Alexandros444/Datenbojen/docs/img/20250713_175419.jpg

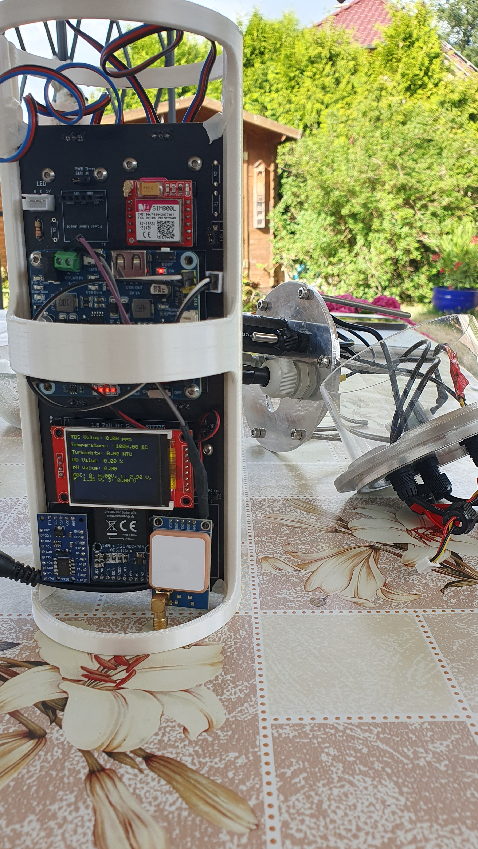
docs/img/20250713_175419.jpg
