Alexandros444/Datenbojen/docs/img/20250718_185127.jpg

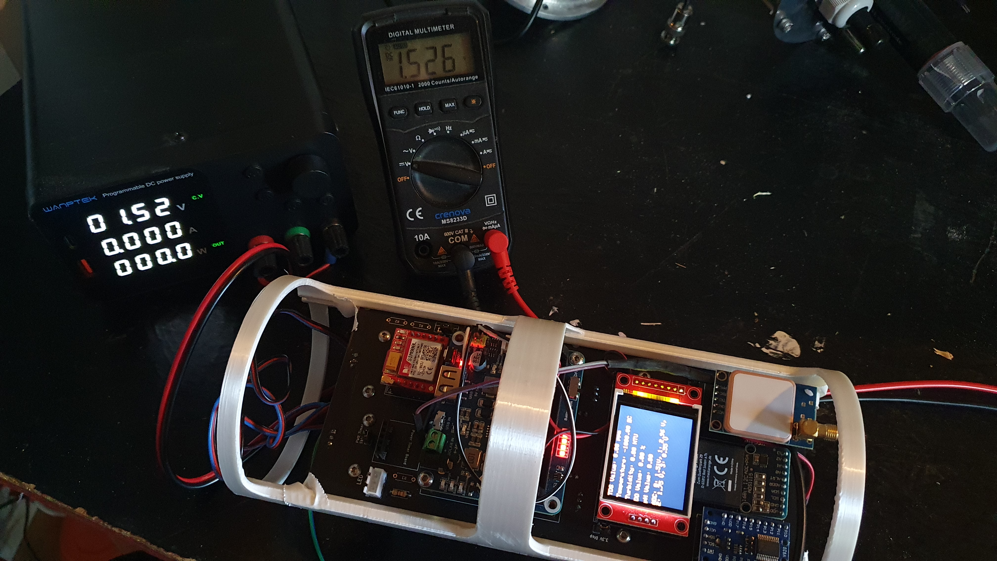
docs/img/20250718_185127.jpg
