Alexandros444/Datenbojen/docs/img/Entwurf/IMG_9408.jpg

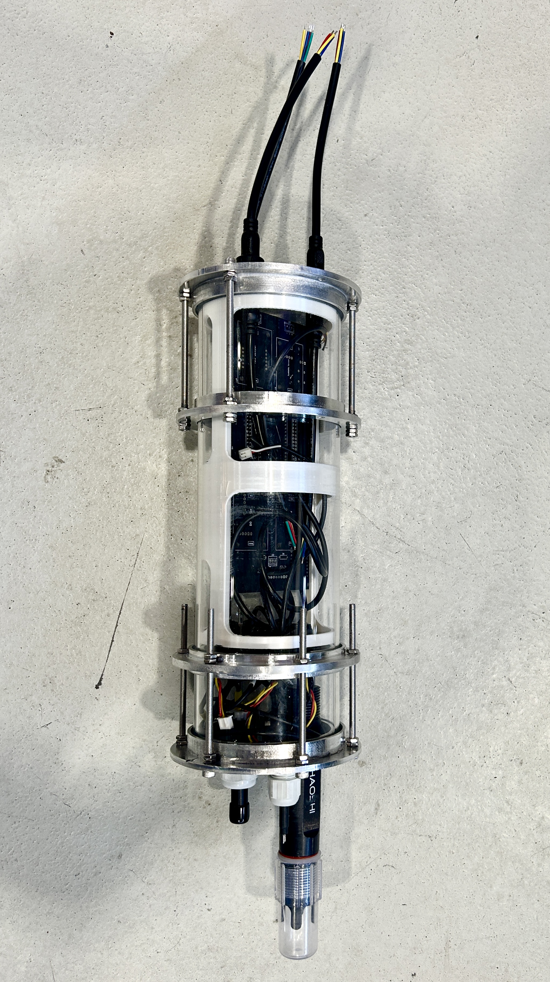
docs/img/Entwurf/IMG_9408.jpg
