Alexandros444/Datenbojen/docs/img/Entwurf/pcb_schematic.png

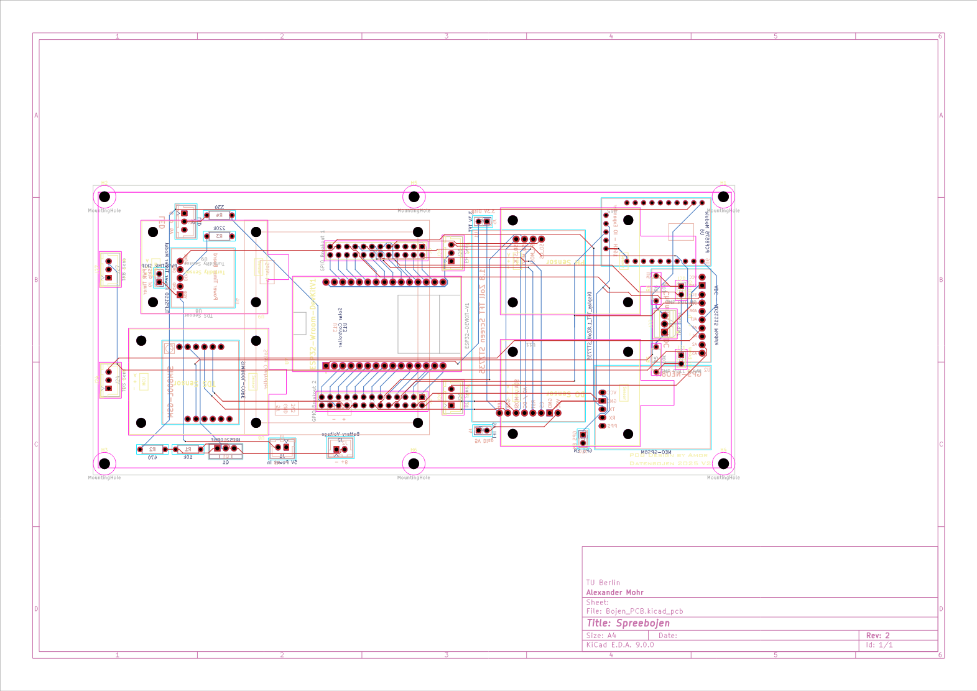
docs/img/Entwurf/pcb_schematic.png
