Alexandros444/Datenbojen/docs/img/Entwurf/pcb_vorderseite.jpg

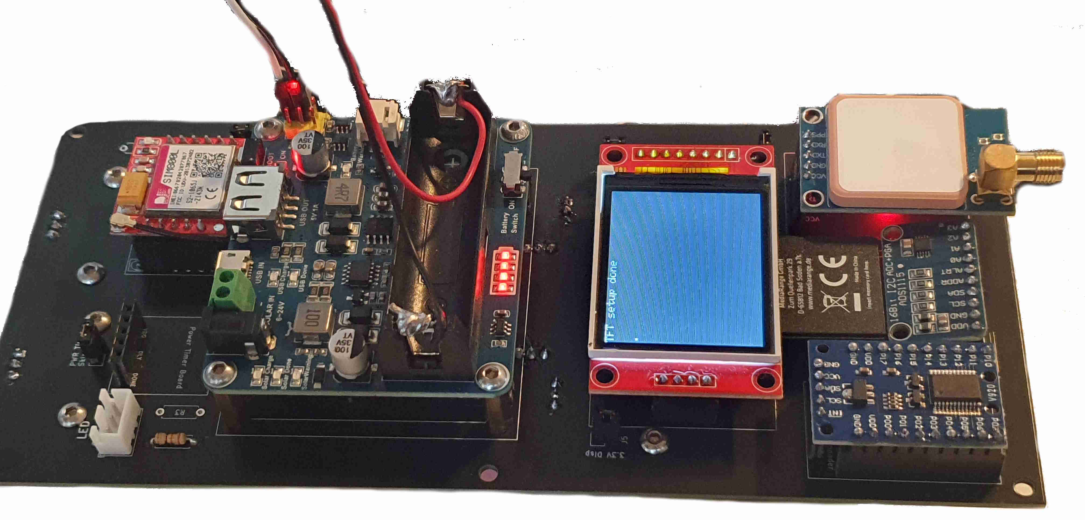
docs/img/Entwurf/pcb_vorderseite.jpg
