Alexandros444/Datenbojen/docs/img/Entwurf/pcb_with_sensors.jpg

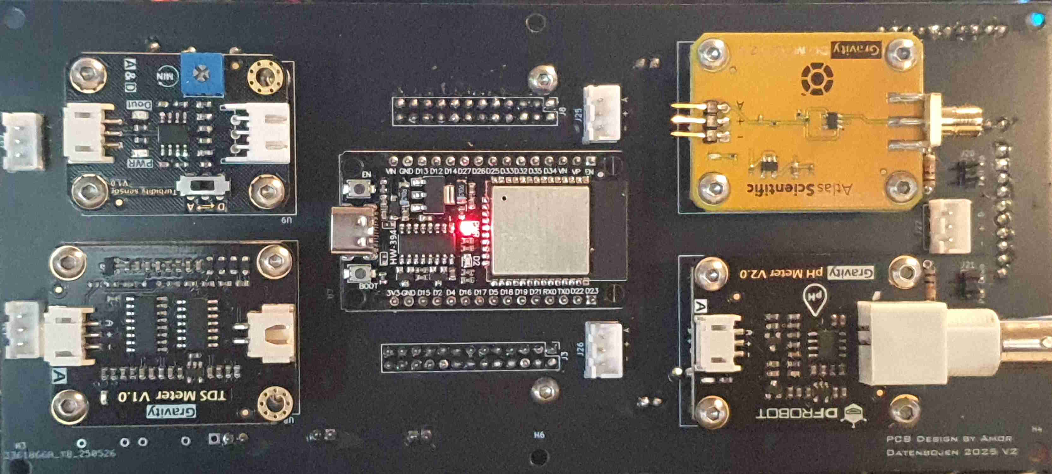
docs/img/Entwurf/pcb_with_sensors.jpg
