Alexandros444/Datenbojen/docs/img/Entwurf/Platine_PCB_Kicad.png

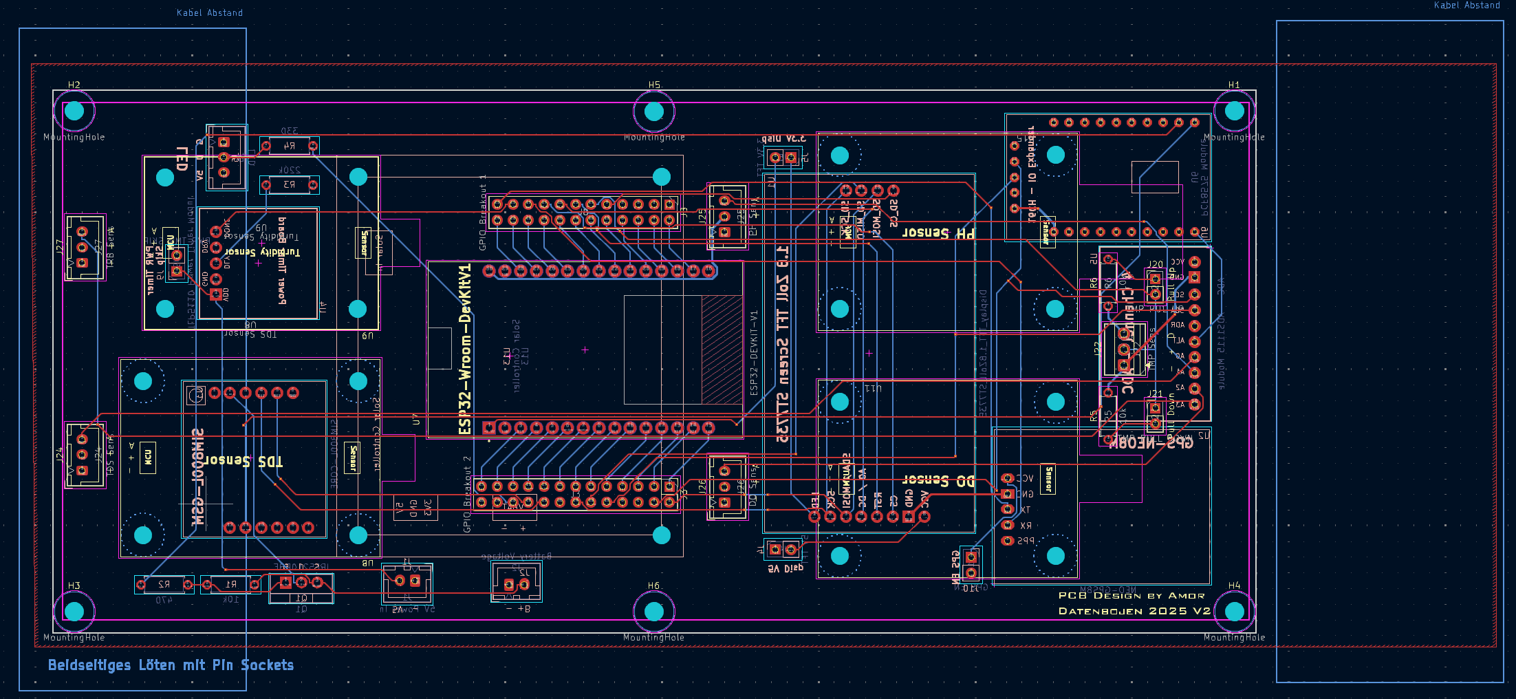
docs/img/Entwurf/Platine_PCB_Kicad.png
