Alexandros444/Datenbojen/docs/img/Entwurf/Platine_PCB_Kicad_3D.png

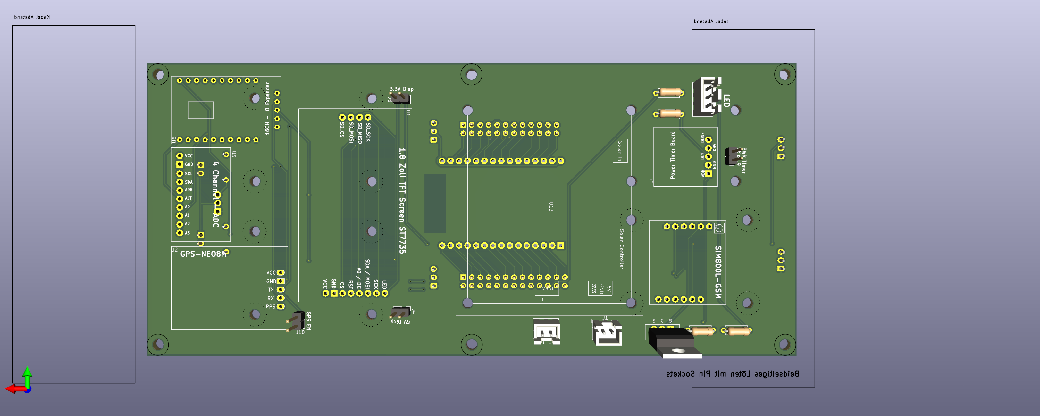
docs/img/Entwurf/Platine_PCB_Kicad_3D.png
