Alexandros444/Datenbojen/docs/img/Entwurf/Platine_PCB_Kicad_3D_render_cut.png

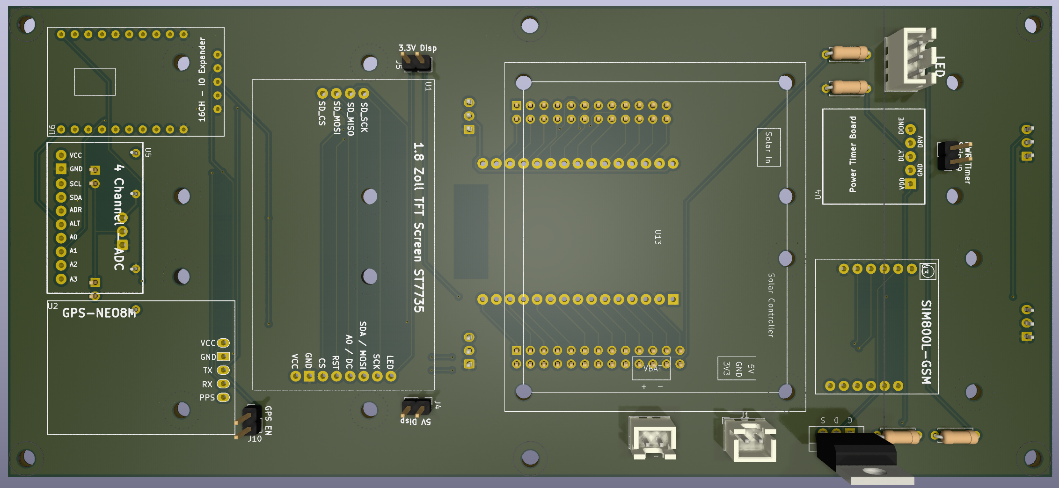
docs/img/Entwurf/Platine_PCB_Kicad_3D_render_cut.png
