Alexandros444/Datenbojen/docs/img/Entwurf/prototyp.jpg

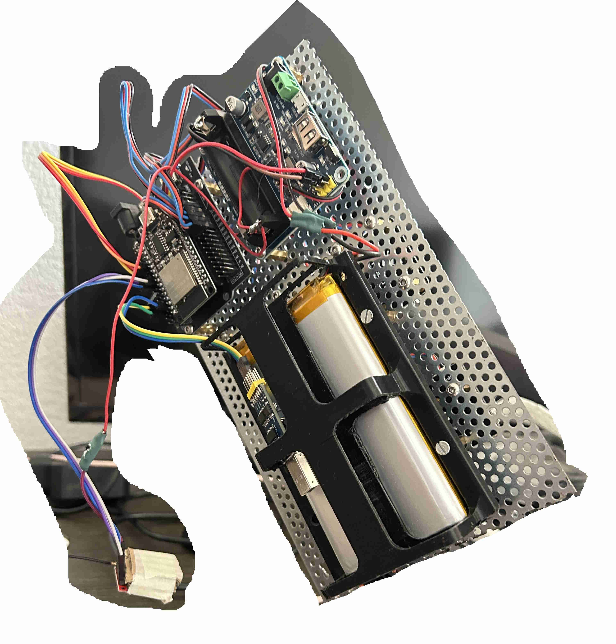
docs/img/Entwurf/prototyp.jpg
