Alexandros444/Datenbojen/docs/img/Entwurf/prototyp_nogb.png

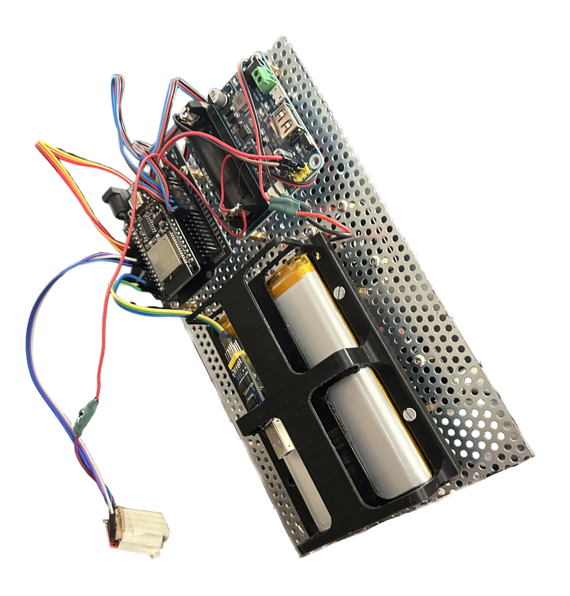
docs/img/Entwurf/prototyp_nogb.png
