Alexandros444/Datenbojen/docs/img/Entwurf/©TheresaMariaForthaus-53677.jpg

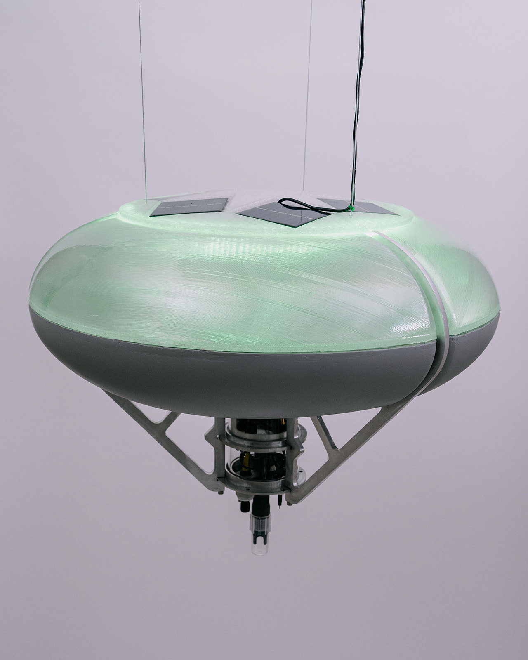
docs/img/Entwurf/©TheresaMariaForthaus-53677.jpg
