Alexandros444/Datenbojen/docs/img/Entwurf/©TheresaMariaForthaus-53696.jpg

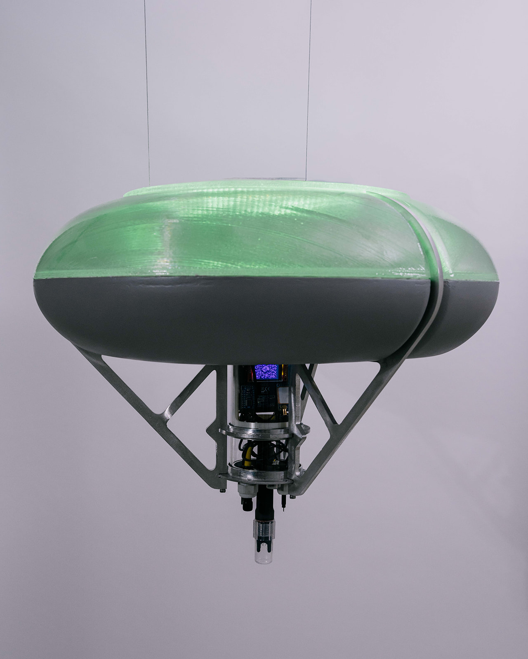
docs/img/Entwurf/©TheresaMariaForthaus-53696.jpg
