Alexandros444/Datenbojen/docs/img/Entwurf/©TheresaMariaForthaus-53716.jpg

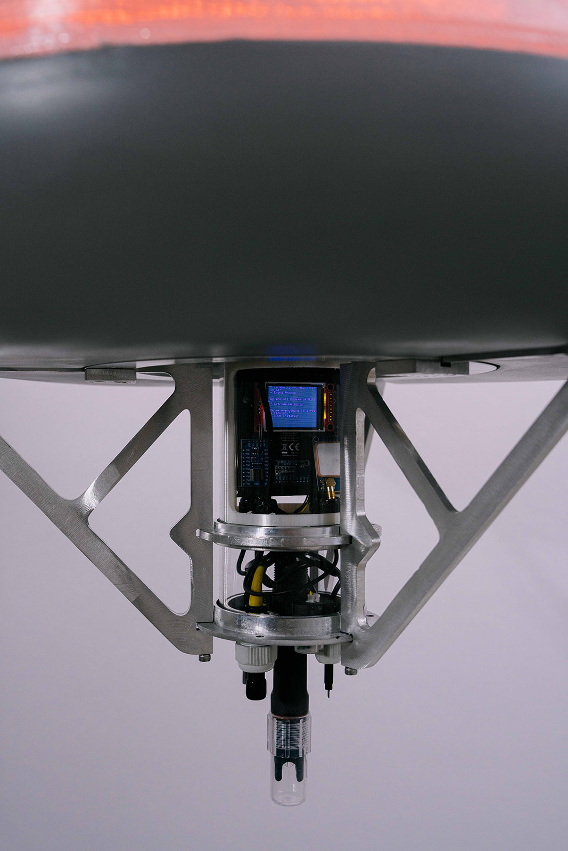
docs/img/Entwurf/©TheresaMariaForthaus-53716.jpg
