Alexandros444/Datenbojen/docs/img/Entwurf/©TheresaMariaForthaus-53720.jpg

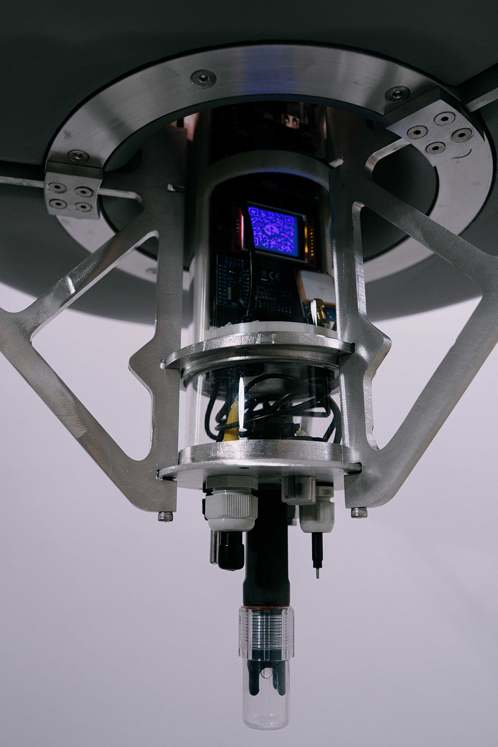
docs/img/Entwurf/©TheresaMariaForthaus-53720.jpg
