Alexandros444/Datenbojen/docs/img/Entwurf/©TheresaMariaForthaus-53730.jpg

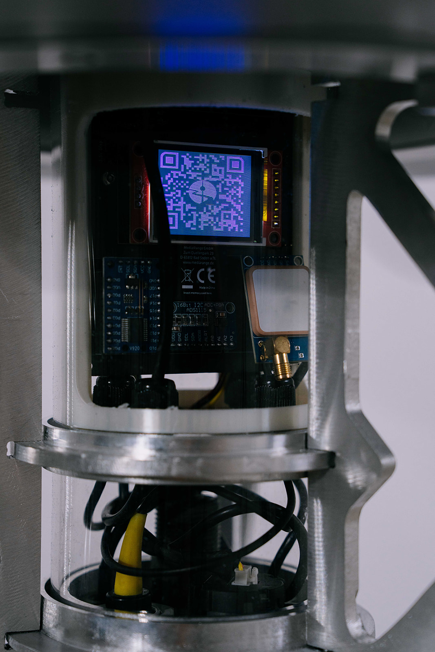
docs/img/Entwurf/©TheresaMariaForthaus-53730.jpg
