Alexandros444/Datenbojen/docs/img/iteration 3/20251018_173604.jpg

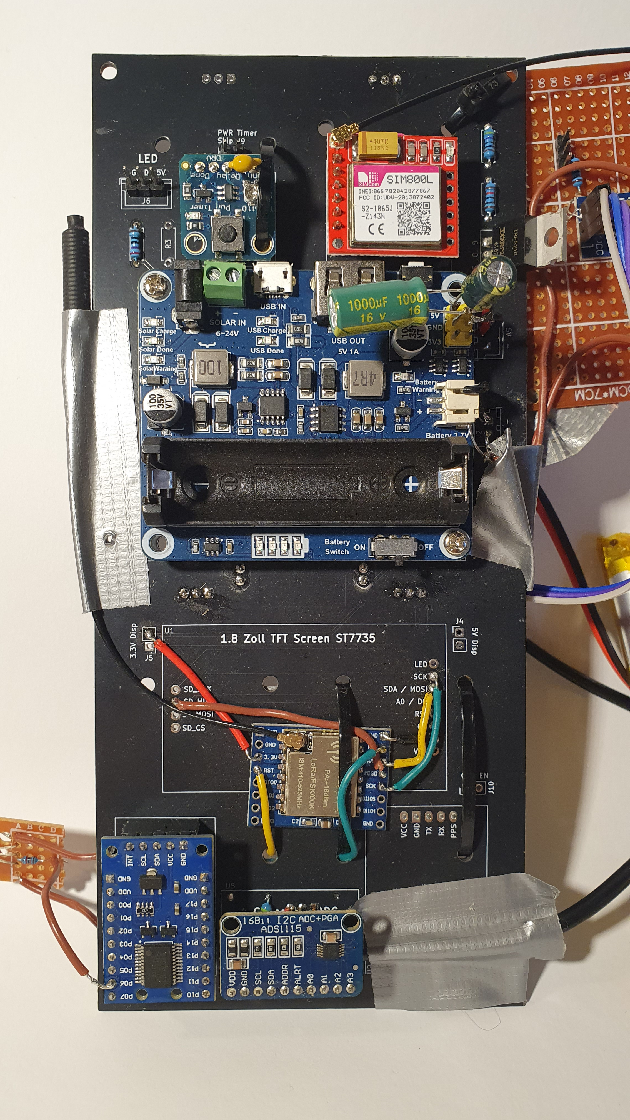
docs/img/iteration 3/20251018_173604.jpg
