Alexandros444/Datenbojen/docs/img/iteration 3/20251018_173955.jpg

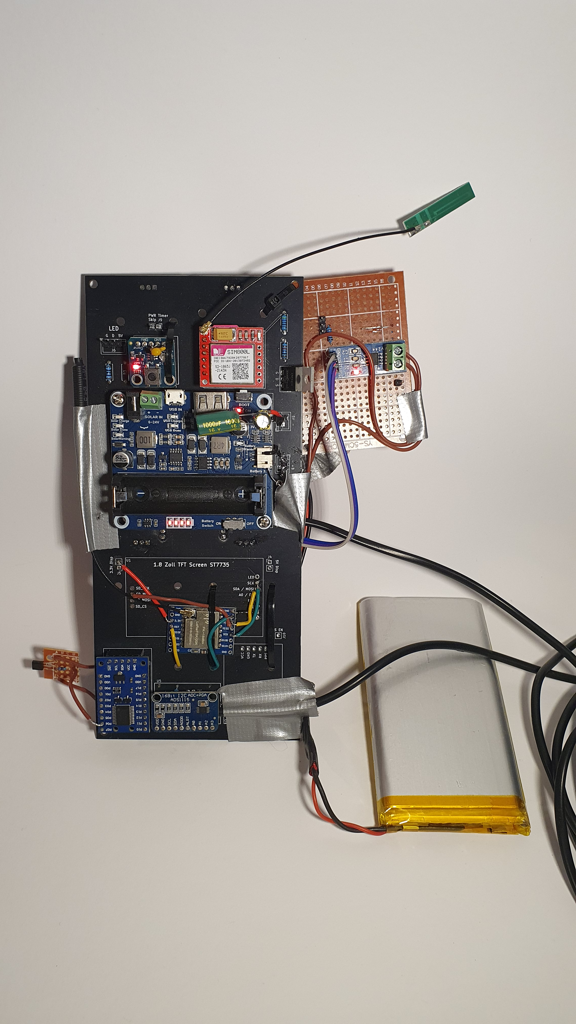
docs/img/iteration 3/20251018_173955.jpg
