Alexandros444/Datenbojen/docs/img/iteration 3/20251018_174100.jpg

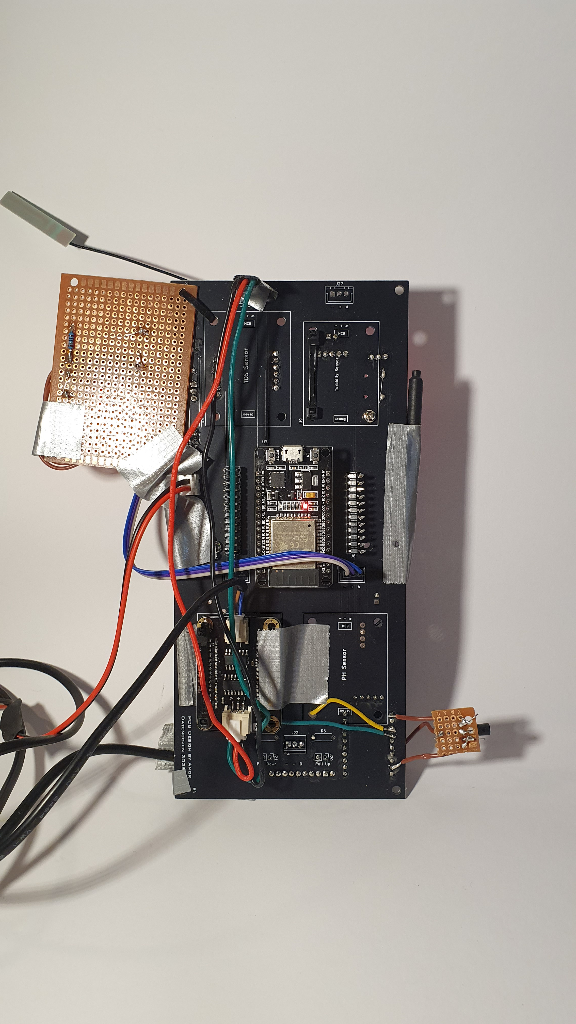
docs/img/iteration 3/20251018_174100.jpg
