Alexandros444/Datenbojen/docs/img/pcb_TPL5110.png

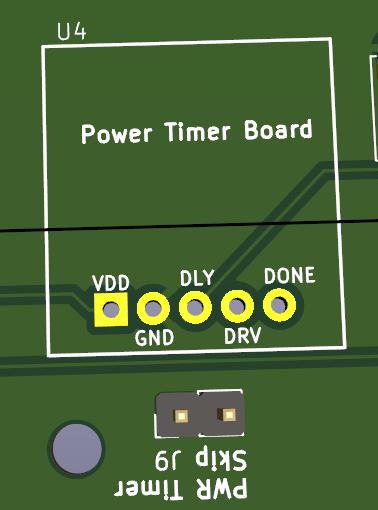
docs/img/pcb_TPL5110.png
