Alexandros444/Datenbojen/docs/img/pcbb.png

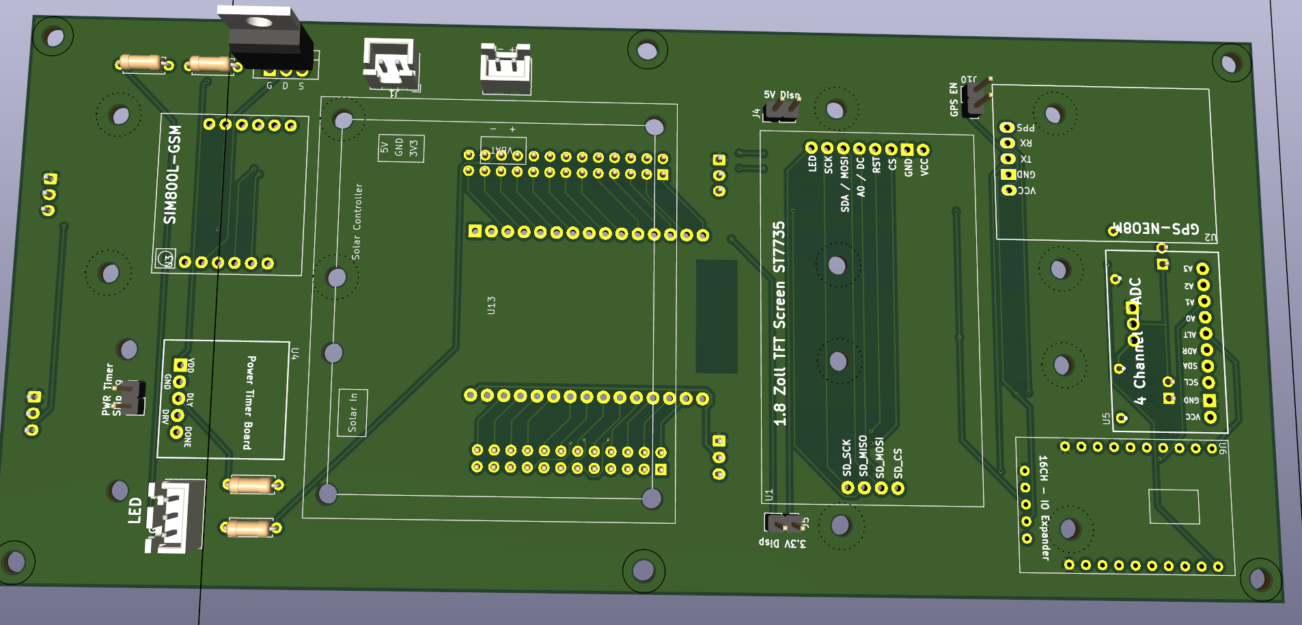
docs/img/pcbb.png
