Alexandros444/Datenbojen/docs/img/pcbf.png

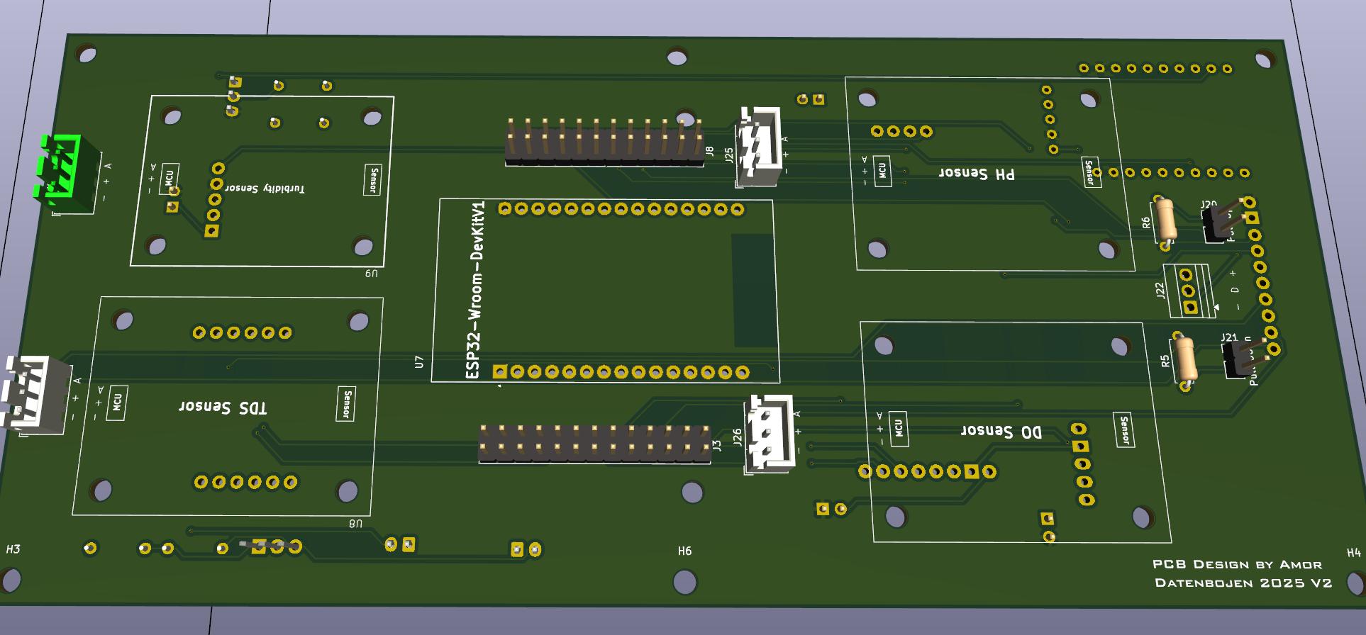
docs/img/pcbf.png
