Alexandros444/Datenbojen/docs/img/schaltplan_esp.png

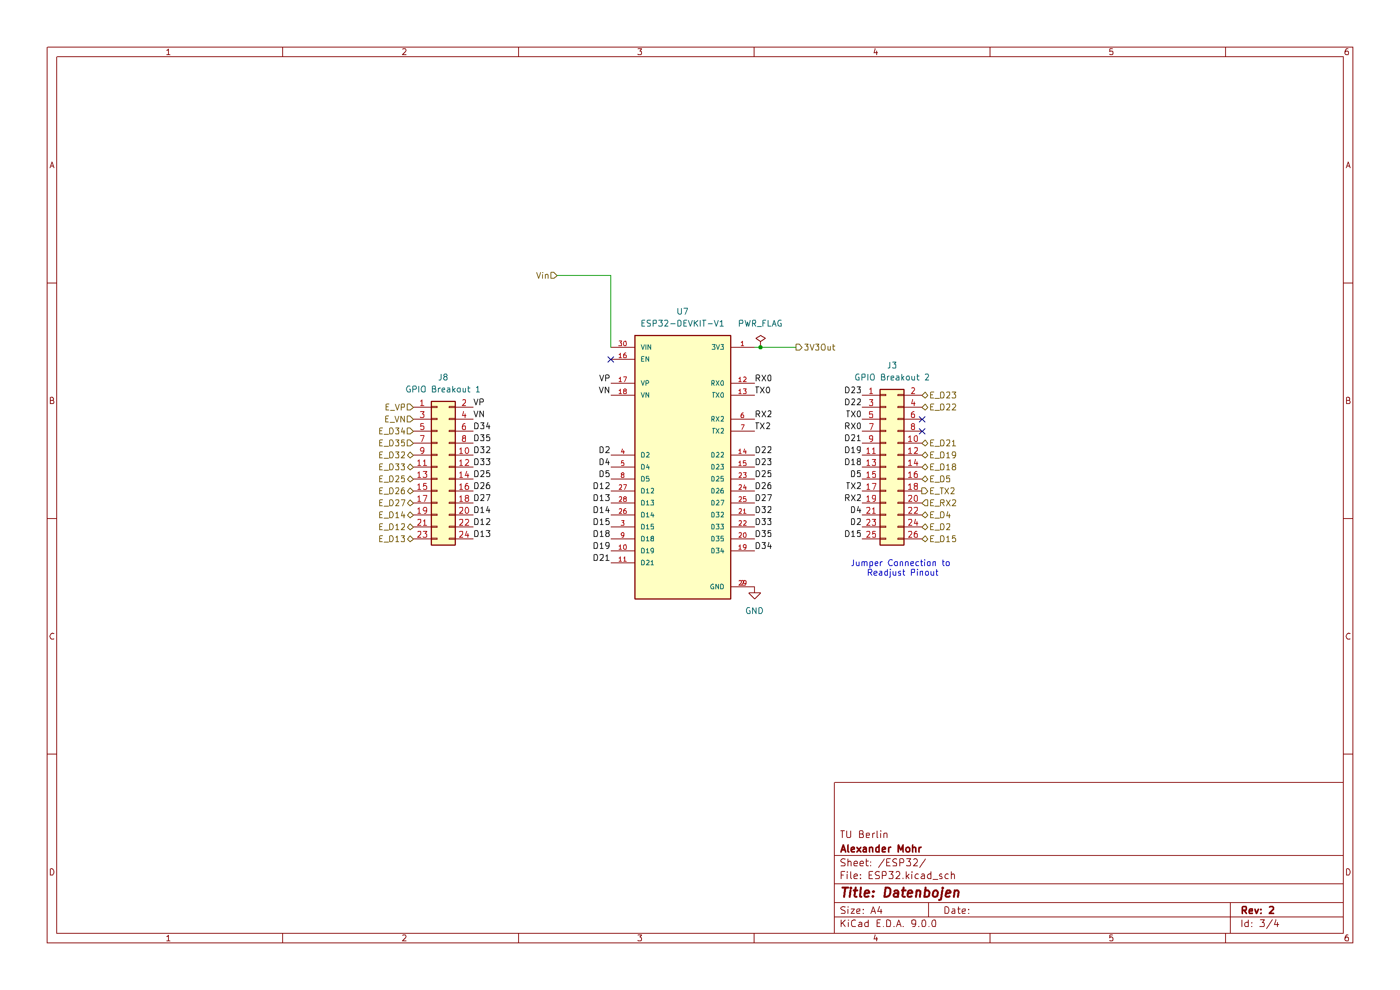
docs/img/schaltplan_esp.png
