Alexandros444/Datenbojen/docs/img/schaltplan_gesamt.png

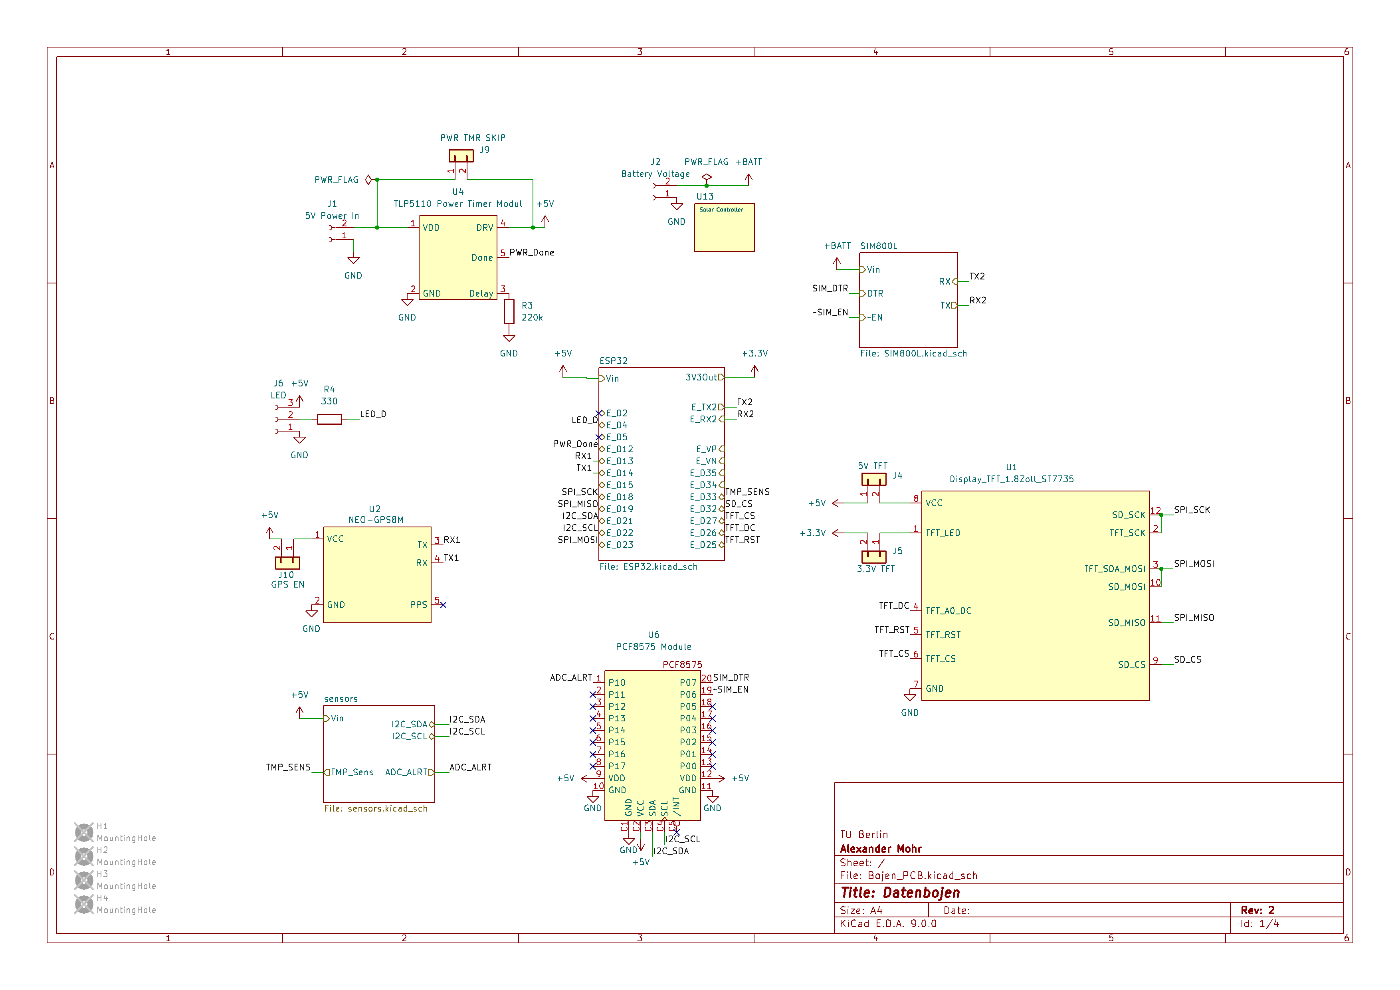
docs/img/schaltplan_gesamt.png
