Alexandros444/Datenbojen/docs/img/schaltplan_sensor.png

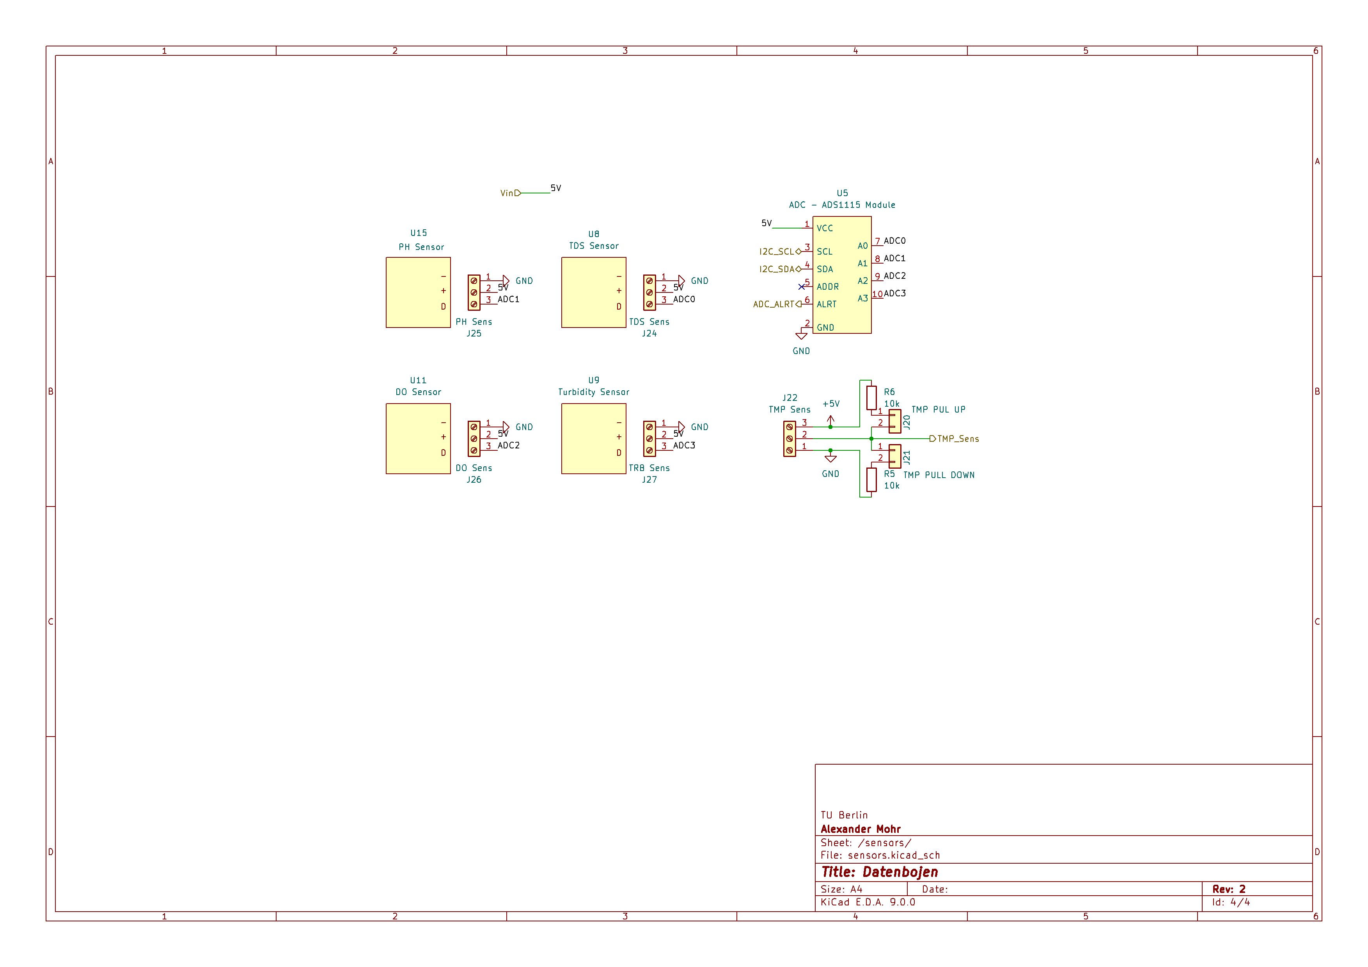
docs/img/schaltplan_sensor.png
