Alexandros444/Datenbojen/docs/img/schaltplan_sim.png

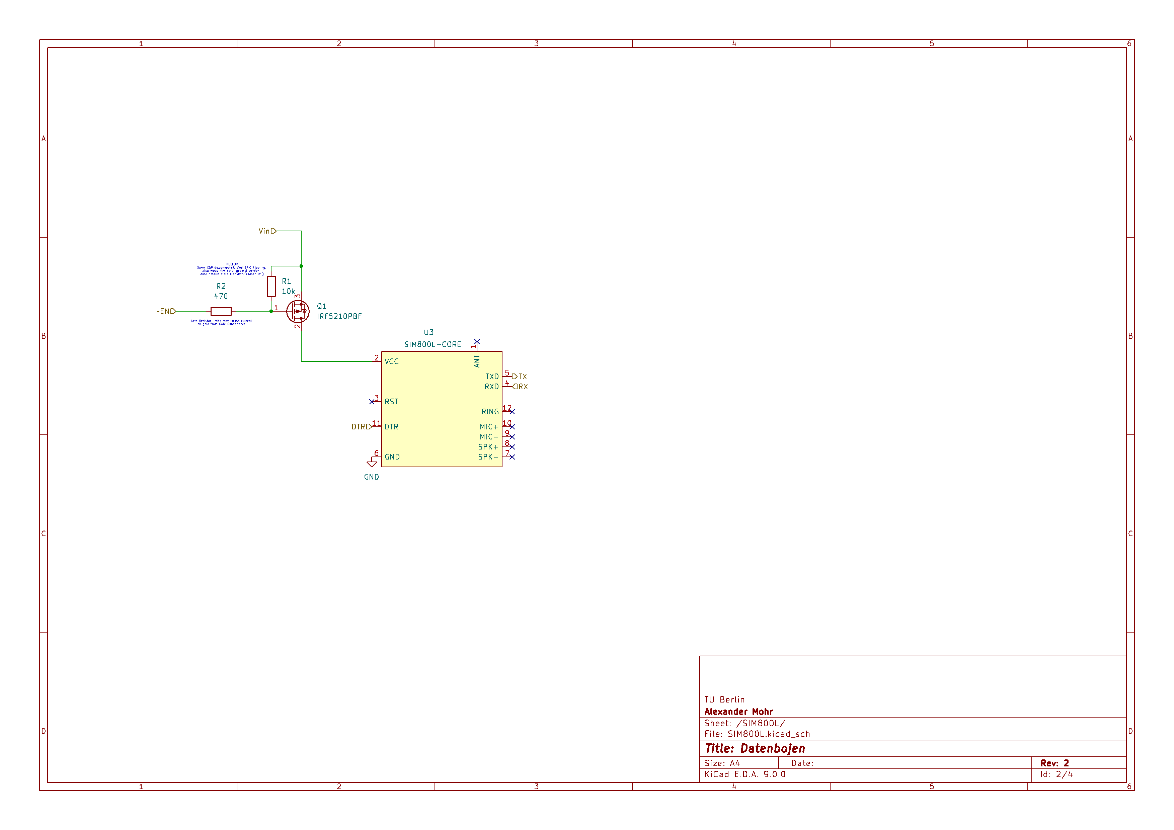
docs/img/schaltplan_sim.png
