Alexandros444/Datenbojen/docs/img/schematic_TPL5110.png

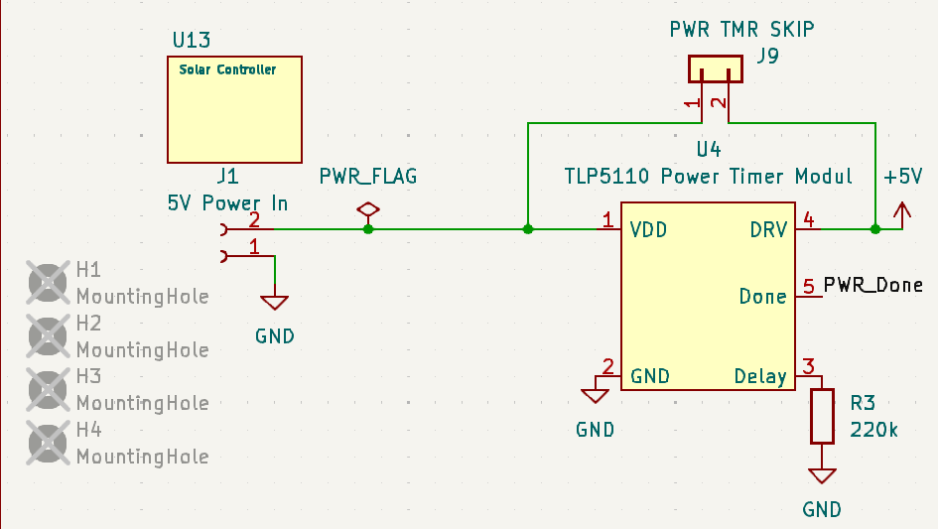
docs/img/schematic_TPL5110.png
