Alexandros444/Datenbojen/docs/img/server_data_plot.png

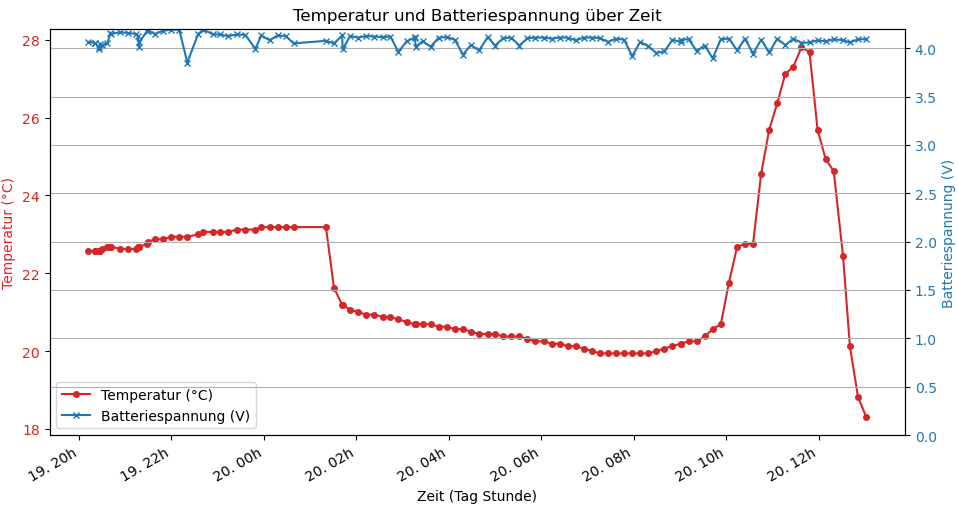
docs/img/server_data_plot.png
