Alexandros444/Datenbojen/docs/img/server_data_plot_2.png

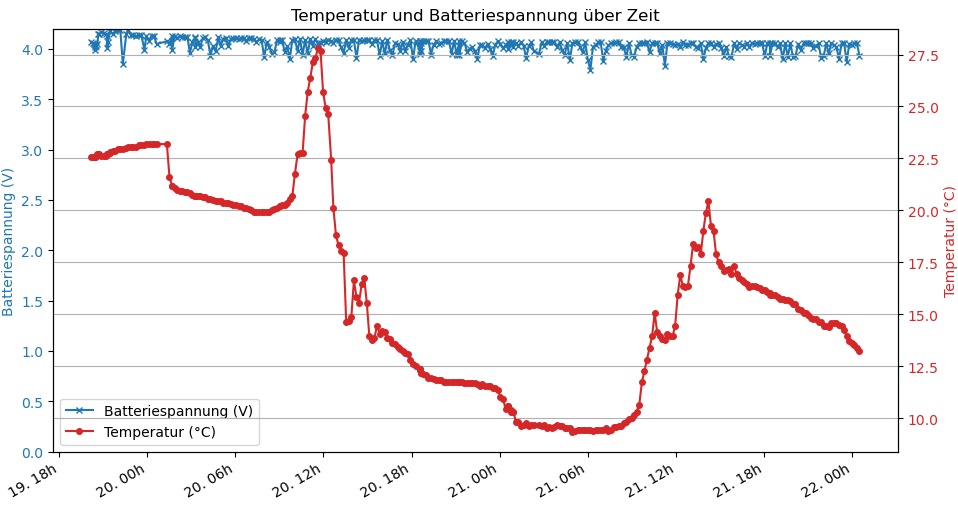
docs/img/server_data_plot_2.png
