Alexandros444/Datenbojen/docs/img/server_data_plot_3.png

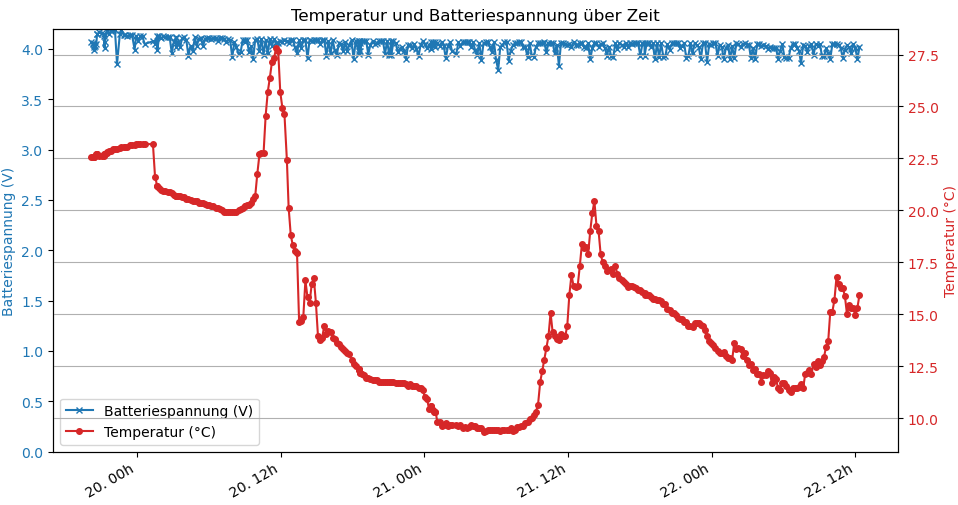
docs/img/server_data_plot_3.png
