Alexandros444/Datenbojen/docs/img/server_data_plot_4.png

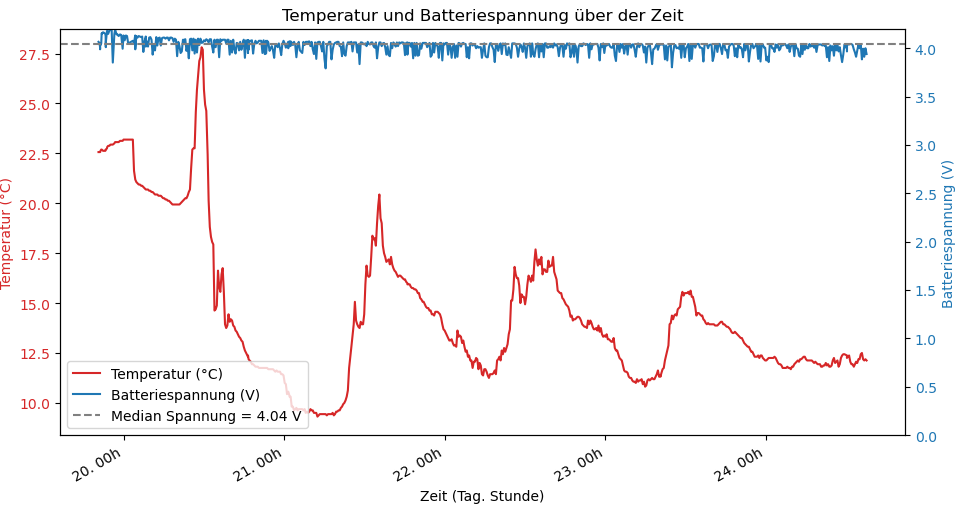
docs/img/server_data_plot_4.png
