Alexandros444/Datenbojen/docs/img/solar_charge_footprint.png

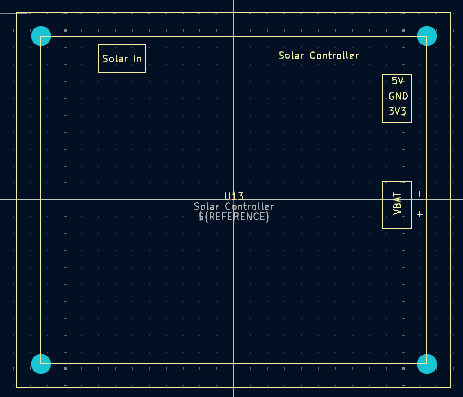
docs/img/solar_charge_footprint.png
