Alexandros444/Datenbojen/docs/img/solar_charge_schematic.png

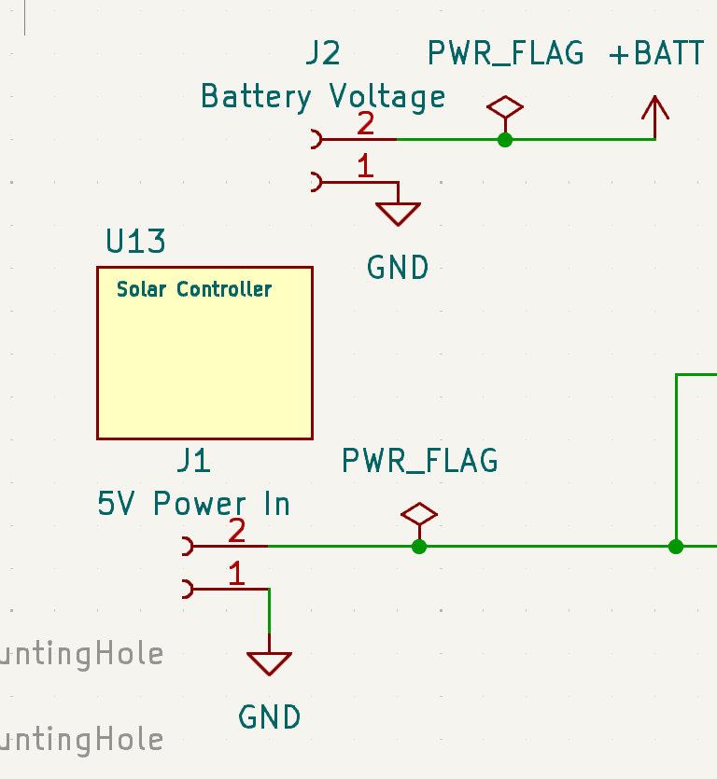
docs/img/solar_charge_schematic.png
