Alexandros444/Datenbojen/docs/img/solarmessung.png

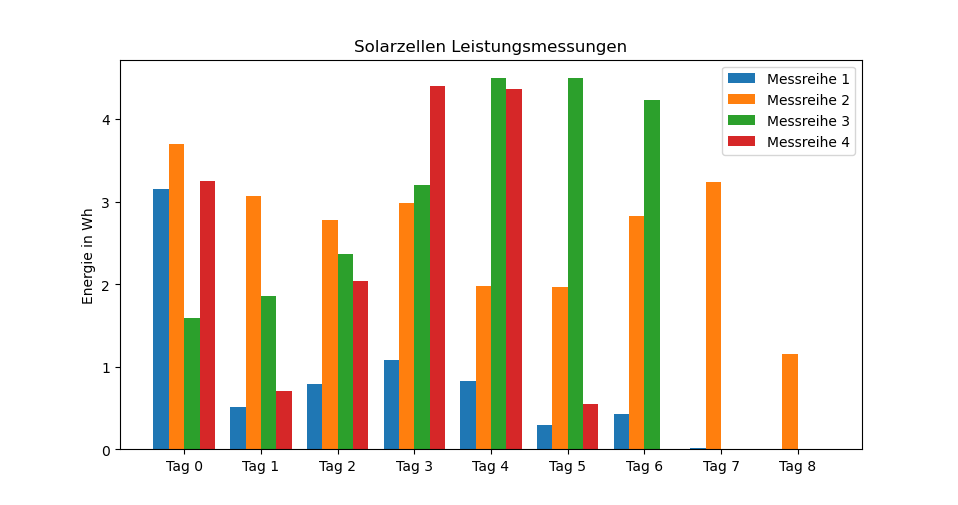
docs/img/solarmessung.png
