Alexandros444/Datenbojen/docs/img/verbrauch_1_messsend.png

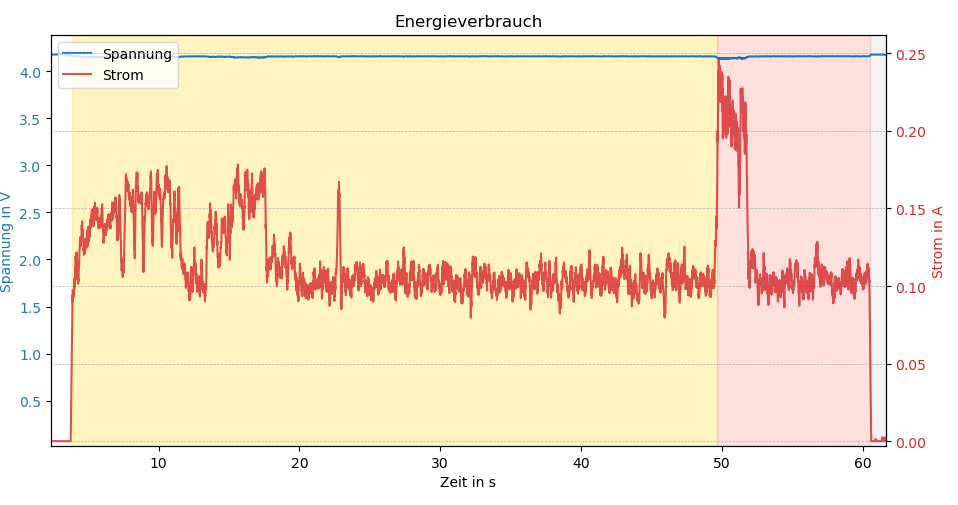
docs/img/verbrauch_1_messsend.png
