Alexandros444/Datenbojen/docs/img/verbrauch_1_zyklus.png

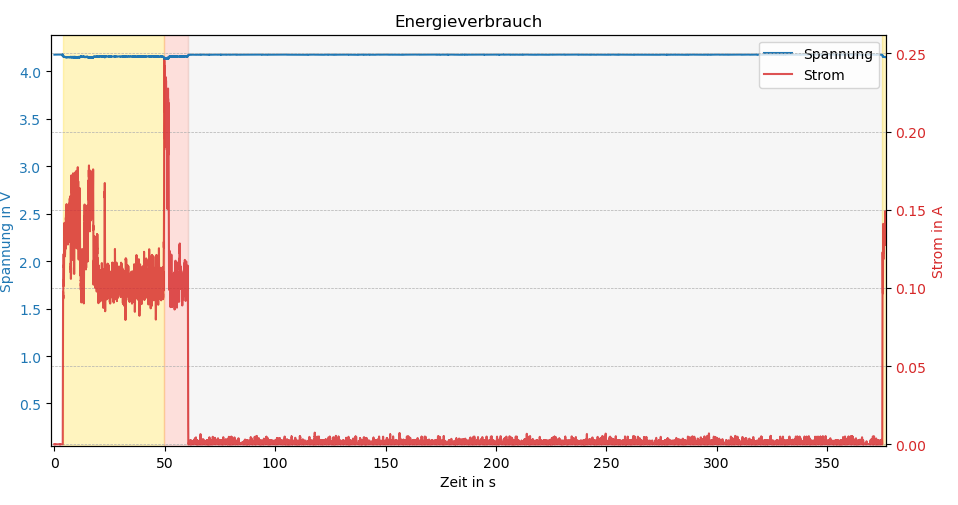
docs/img/verbrauch_1_zyklus.png
