Alexandros444/Datenbojen/docs/img/verbrauch_1_zyklus_mittel.png

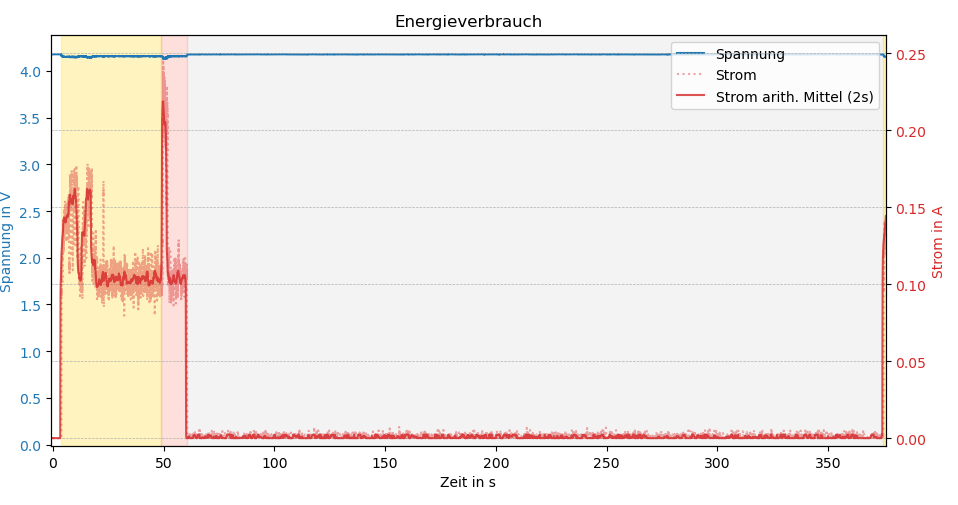
docs/img/verbrauch_1_zyklus_mittel.png
