Alexandros444/Datenbojen/docs/img/verbrauch_3_zyklen2.png

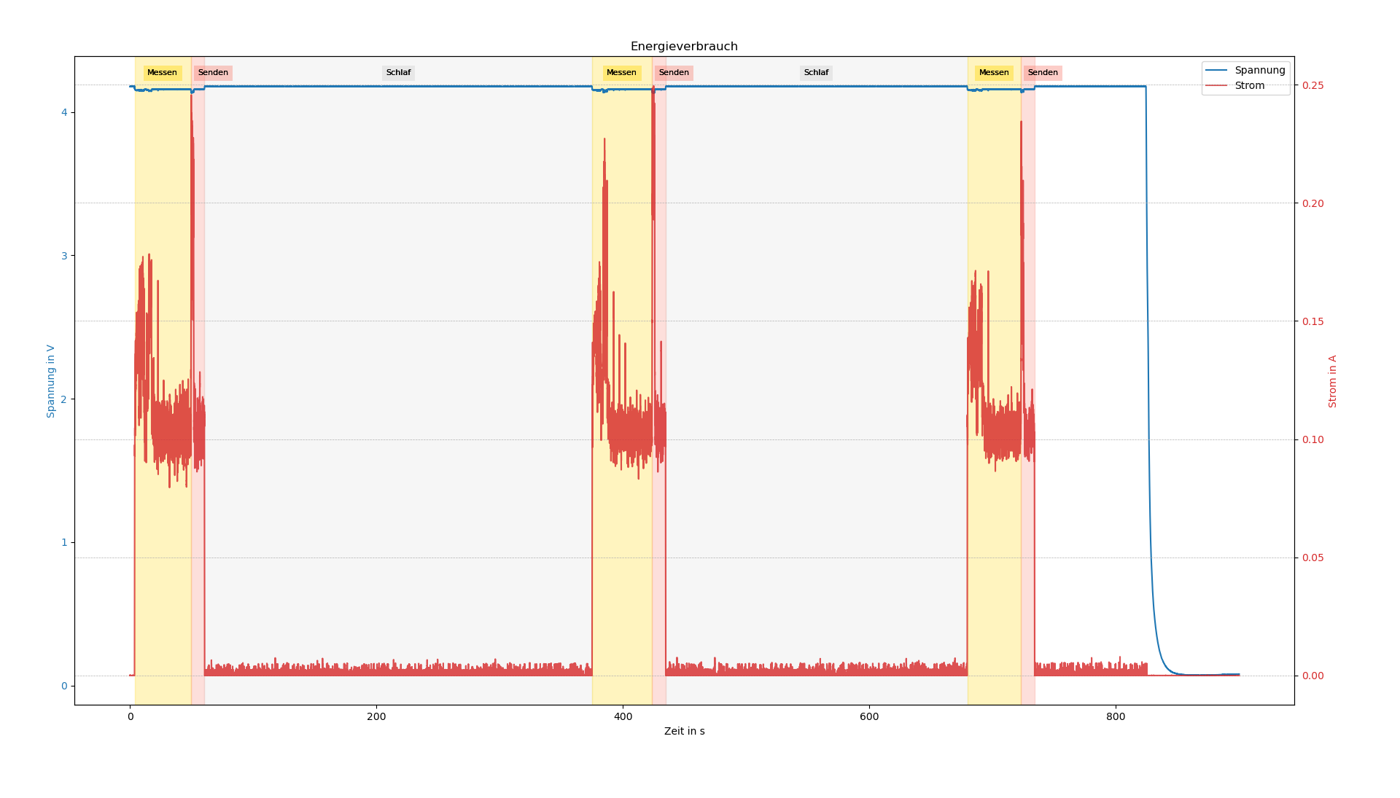
docs/img/verbrauch_3_zyklen2.png
