Alexandros444/Datenbojen/docs/img/verbrauch_3_zyklen_mittel.png

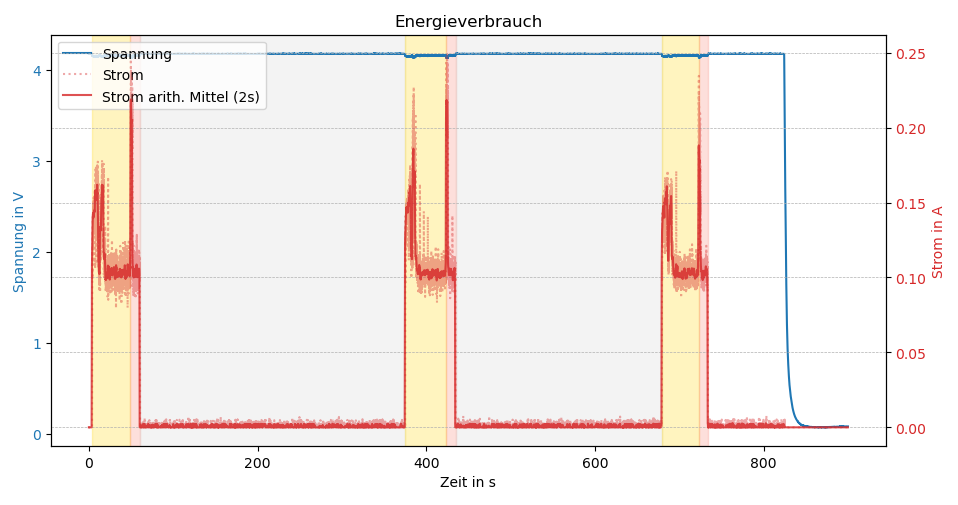
docs/img/verbrauch_3_zyklen_mittel.png
