Alexandros444/Datenbojen/docs/img/verbrauch_3_zyklen_mittel_cut.png

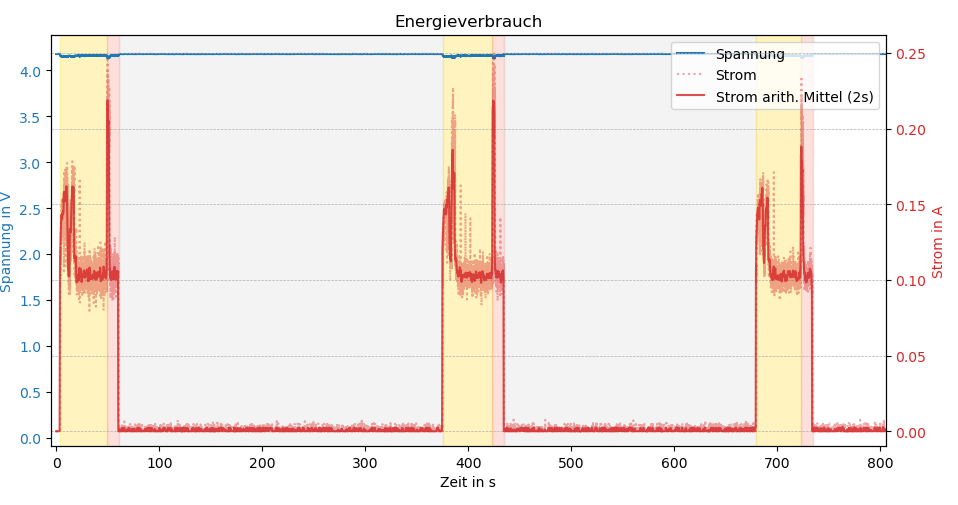
docs/img/verbrauch_3_zyklen_mittel_cut.png
