Alexandros444/Datenbojen/docs/img/verbrauch_3_zyklen_no_drop.png

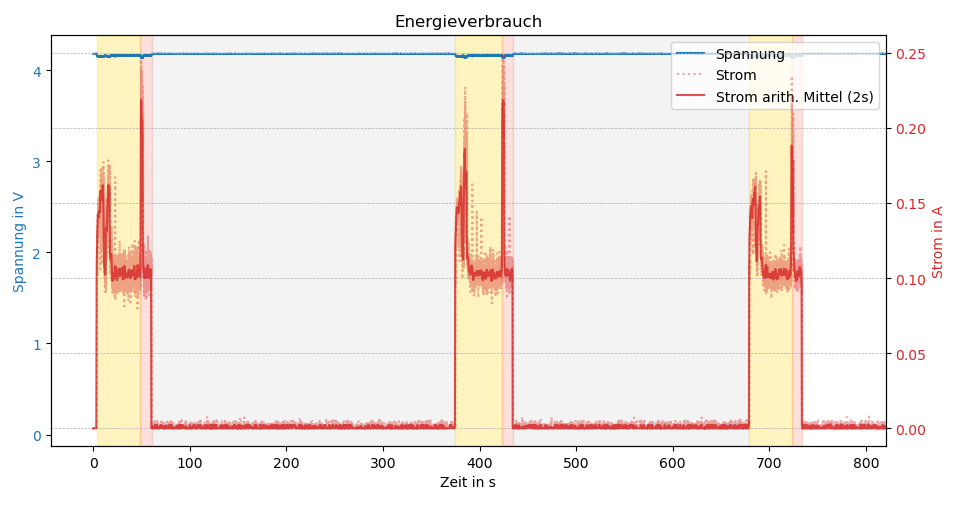
docs/img/verbrauch_3_zyklen_no_drop.png
