Alexandros444/Datenbojen/docs/img/verbrauch_akkumuliert_1_zyklus.png

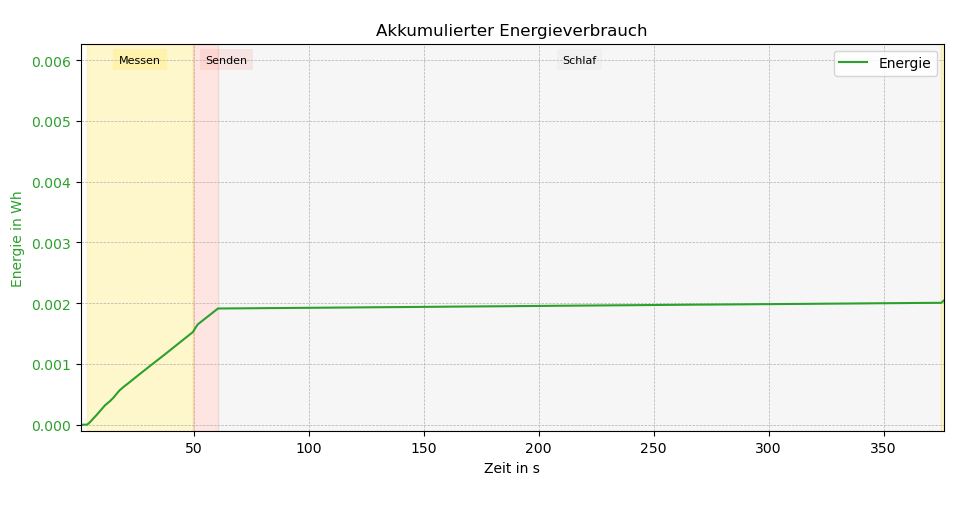
docs/img/verbrauch_akkumuliert_1_zyklus.png
