Alexandros444/Datenbojen/docs/img/verbrauch_akkumuliert_3_zyklen.png

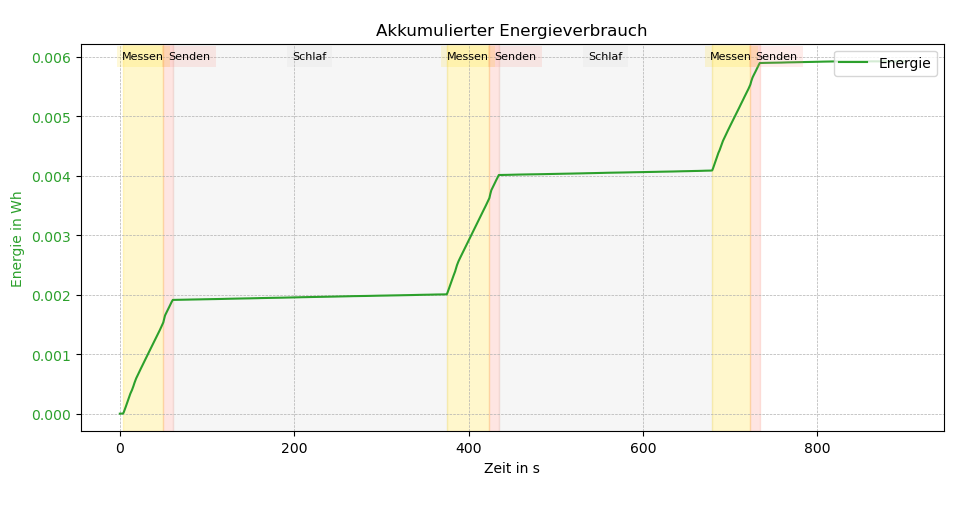
docs/img/verbrauch_akkumuliert_3_zyklen.png
