Alexandros444/Datenbojen/docs/img/verbrauch_akkumuliert_3_zyklen_cut.png

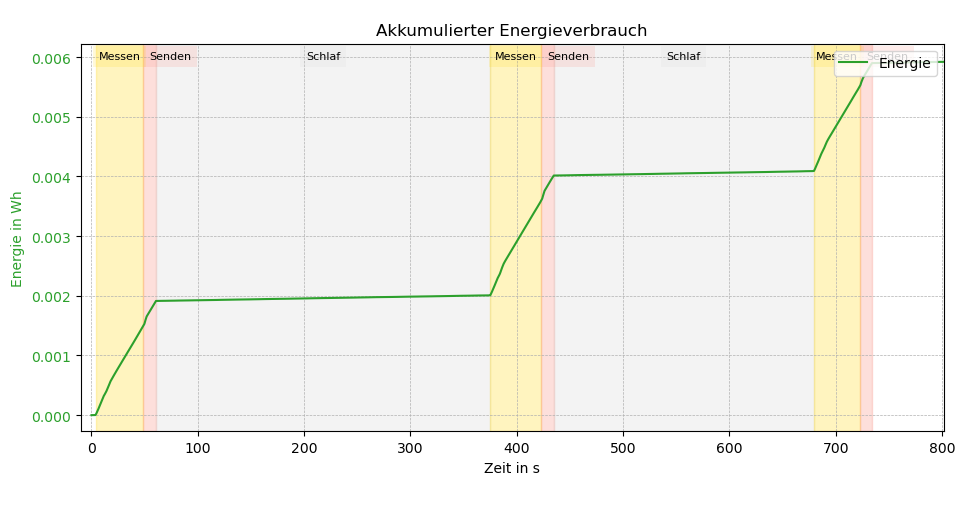
docs/img/verbrauch_akkumuliert_3_zyklen_cut.png
