Alexandros444/Datenbojen/docs/Systementwurf/blockschaltbild_3.drawio.png

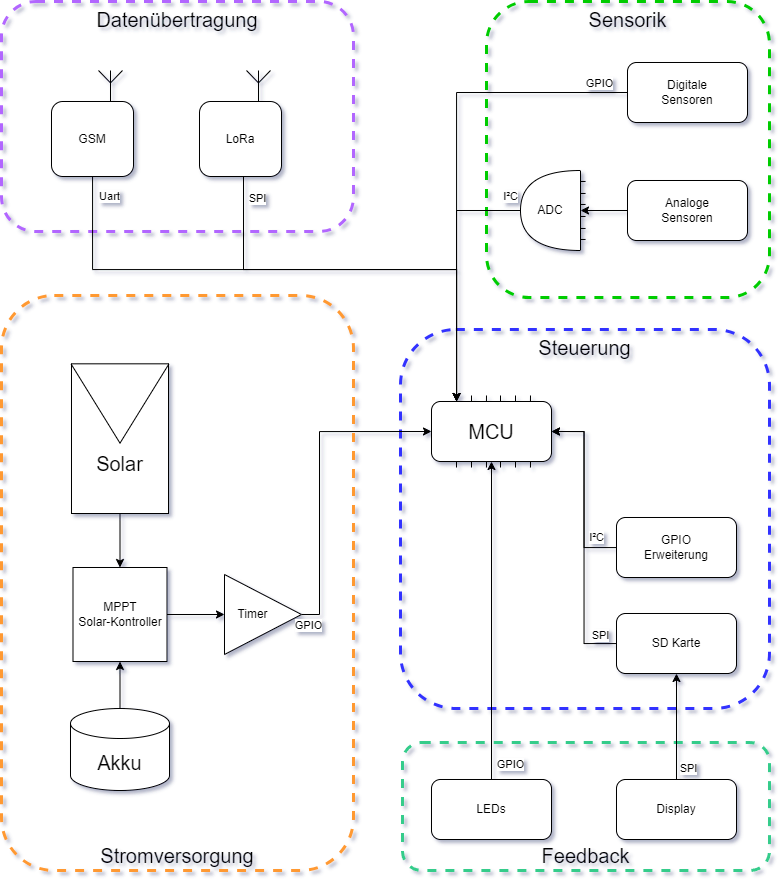
docs/Systementwurf/blockschaltbild_3.drawio.png
