Alexandros444/Datenbojen/docs/Systementwurf/blockschaltbild_4.drawio.png

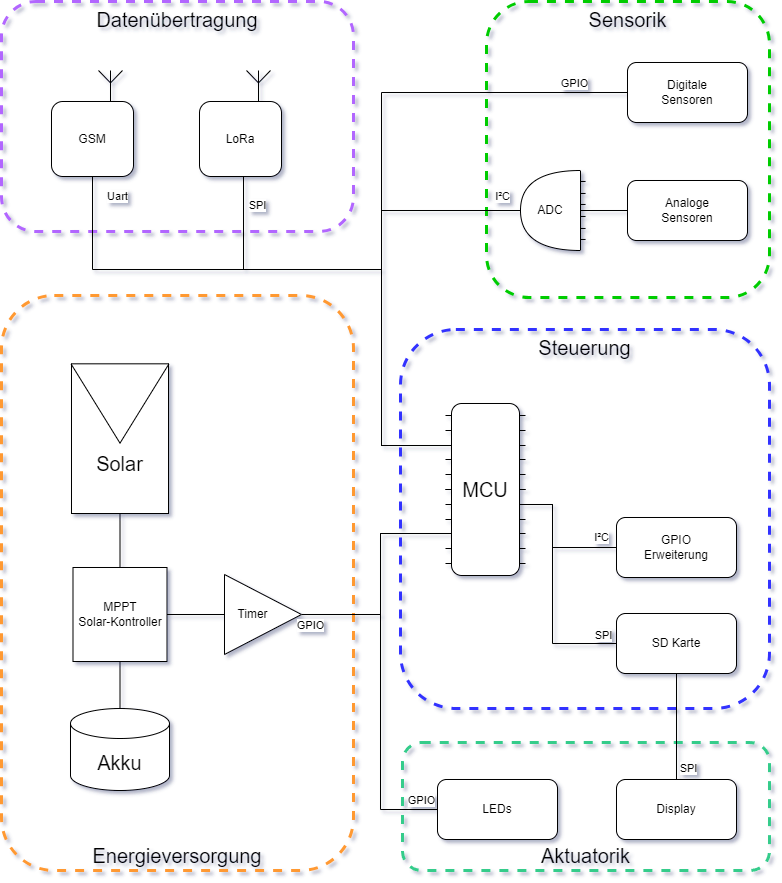
docs/Systementwurf/blockschaltbild_4.drawio.png
