Alexandros444/Datenbojen/docs/Systementwurf/GSM_LoRa_Connection.drawio.png

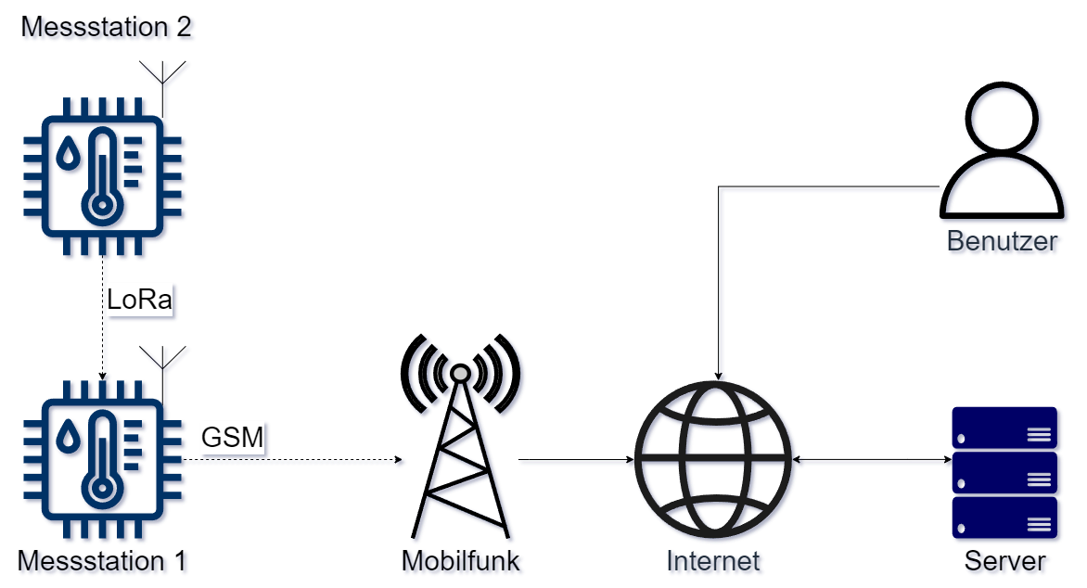
docs/Systementwurf/GSM_LoRa_Connection.drawio.png
