Alexandros444/Datenbojen/docs/Systementwurf/GSM_LoRa_Connection_top.drawio.png

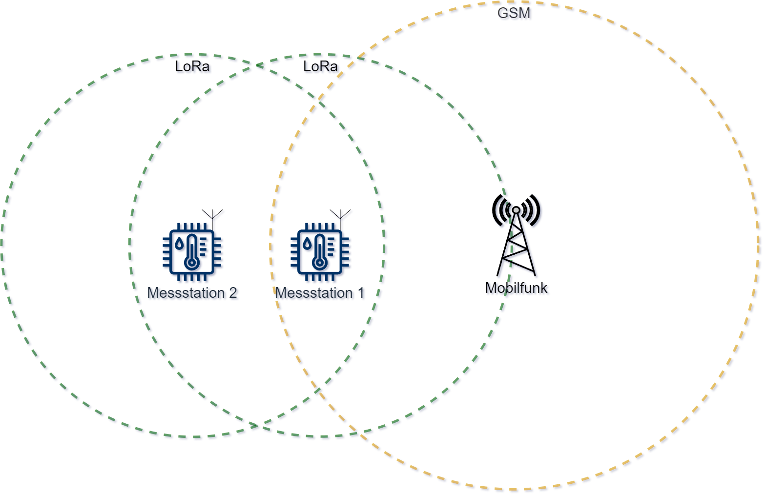
docs/Systementwurf/GSM_LoRa_Connection_top.drawio.png
