Alexandros444/Datenbojen/hardware/KiCad Files/KiCad_IC_Footprint/tds_sensor_image.png

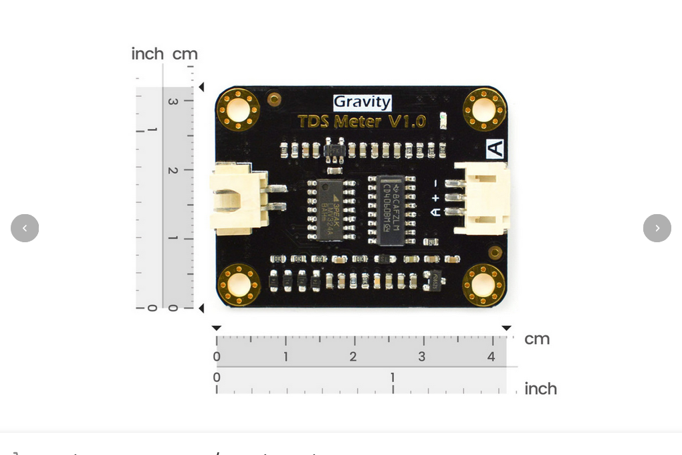
hardware/KiCad Files/KiCad_IC_Footprint/tds_sensor_image.png
