Alexandros444/Datenbojen/src/Server/temp_voltage_plot.png

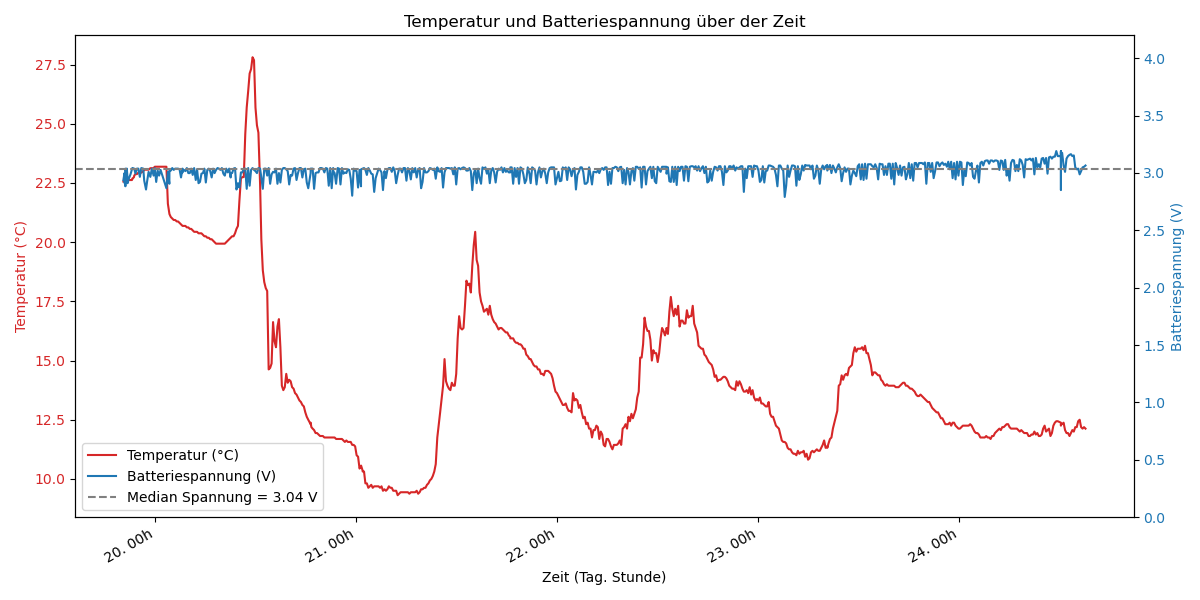
src/Server/temp_voltage_plot.png
