Alexandros444/Datenbojen/docs/img/Entwurf/boje_aufbau_nobg.png

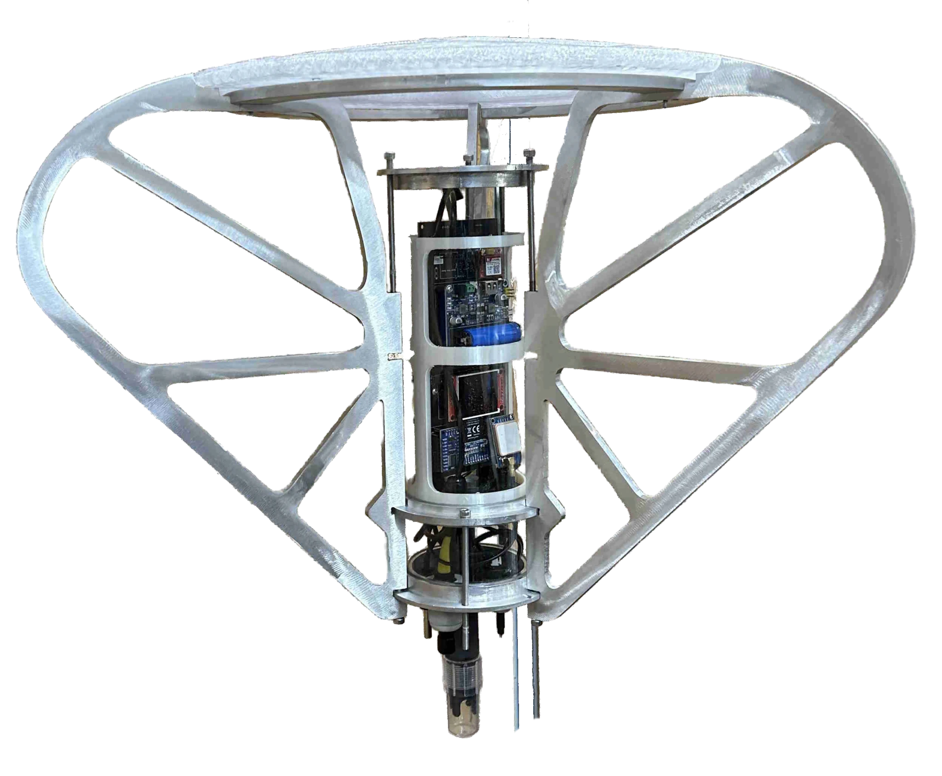
docs/img/Entwurf/boje_aufbau_nobg.png
