Alexandros444/Datenbojen/docs/Tests/SystemTests/SystemTestLong2_cycle_summary.csv

cycle | t_start_s | t_send_s | t_end_s | dur_measure_s | dur_send_s | dur_sleep_s | mean_power_measure_W | mean_power_send_W | energy_consumed_Wh
1 | 1.63 | 21.92 | 45.78 | 20.290000000000003 | 23.86 | 583.36 | 0.5507373833825037 | 0.6068131290461668 | 0.0017817199999999999
2 | 629.14 | 649.14 | 672.94 | 20.0 | 23.800000000000068 | 583.76 | 0.5618699182987 | 0.5808950252026039 | 0.00174068
3 | 1256.7 | 1276.93 | 1301.56 | 20.230000000000018 | 24.62999999999988 | 0.0 | 0.599305805184874 | 0.5927587643482548 | 0.00185602
