Alexandros444/Datenbojen/docs/Tests/SystemTests/SystemTestLong3.csv

# 100.0 sps | start/stop: 50/0 mA (5 s) | channels: 5
# V min: 4.0689 | V max: 4.14513
# I min: 0.0 | I max: 0.30239
# P min: 0.0 | P max: 1.2334699773
Time | Voltage | Current | Power | Capacity | Energy
0.00000000 | 4.14450000 | 0.00246000 | 0.01019547 | 0.00000000 | 0.00000001
0.01000000 | 4.14434000 | 0.00249000 | 0.01031941 | 0.00000001 | 0.00000001
0.02000000 | 4.14434000 | 0.00243000 | 0.01007075 | 0.00000002 | 0.00000002
0.03000000 | 4.14419000 | 0.00504000 | 0.02088672 | 0.00000003 | 0.00000004
0.04000000 | 4.14419000 | 0.00507000 | 0.02101104 | 0.00000004 | 0.00000005
0.05000000 | 4.14403000 | 0.00511000 | 0.02117599 | 0.00000006 | 0.00000006
0.06000000 | 4.14403000 | 0.00511000 | 0.02117599 | 0.00000007 | 0.00000008
0.07000000 | 4.14387000 | 0.00511000 | 0.02117518 | 0.00000008 | 0.00000009
0.08000000 | 4.14372000 | 0.00517000 | 0.02142303 | 0.00000010 | 0.00000011
0.09000000 | 4.14372000 | 0.00523000 | 0.02167166 | 0.00000011 | 0.00000012
0.10000000 | 4.14372000 | 0.00520000 | 0.02154734 | 0.00000013 | 0.00000014
0.11000000 | 4.14387000 | 0.00514000 | 0.02129949 | 0.00000014 | 0.00000015
0.12000000 | 4.14372000 | 0.00237000 | 0.00982062 | 0.00000015 | 0.00000016
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
