Alexandros444/Datenbojen/docs/Tests/SystemTests/SystemTestLong3_unknown_cycles.csv

cycle | t_start_s | t_send_s | t_end_s | dur_measure_s | dur_send_s | dur_sleep_s | mean_power_measure_mW | mean_power_send_mW | mean_power_sleep_mW | total_energy_meas_Ws | total_energy_send_Ws | total_energy_sleep_Ws | total_energy_cycle_Ws | cycle_duration_s
1 | 3.97 | 47.65 | 47.65 | 43.68 | 0.0 | 0.0 | 580.4759490724816 | 144.5842232 | 0.0 | 25.353029935921 | 0.0 | 0.0 | 25.353029935921 | 43.68
