Alexandros444/Datenbojen/docs/Tests/SolarTests/Batterie-Ladezustand_1.png

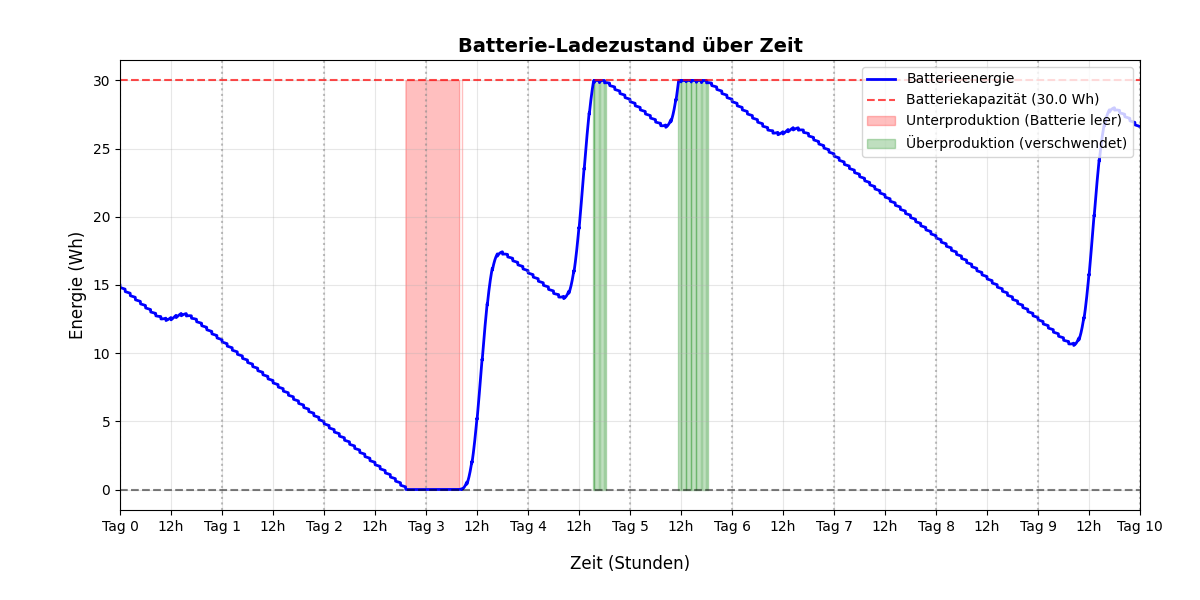
docs/Tests/SolarTests/Batterie-Ladezustand_1.png
