Alexandros444/Datenbojen/docs/Tests/SolarTests/Leistungsaufnahme.png

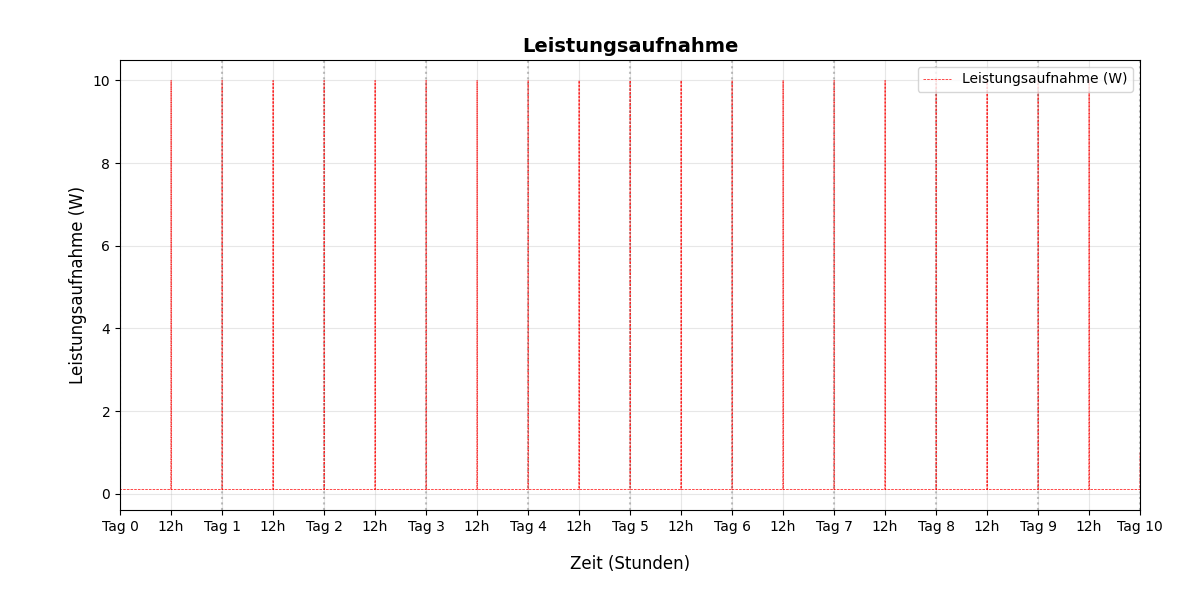
docs/Tests/SolarTests/Leistungsaufnahme.png
