Alexandros444/Datenbojen/docs/Tests/SolarTests/Solar_leistung.png

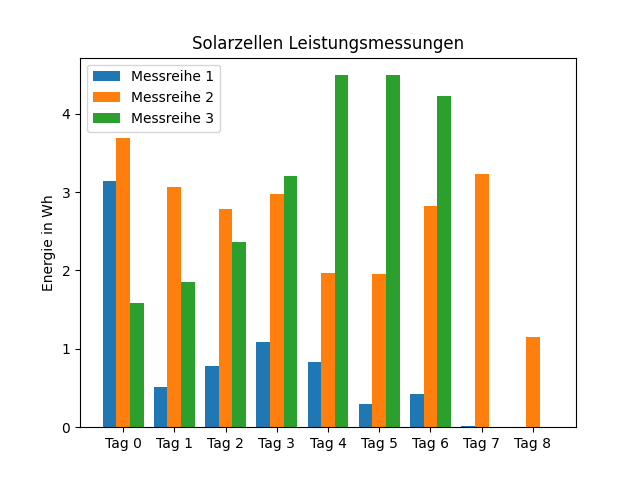
docs/Tests/SolarTests/Solar_leistung.png
