Alexandros444/Datenbojen/docs/Tests/SolarTests/Solarertrag_1.png

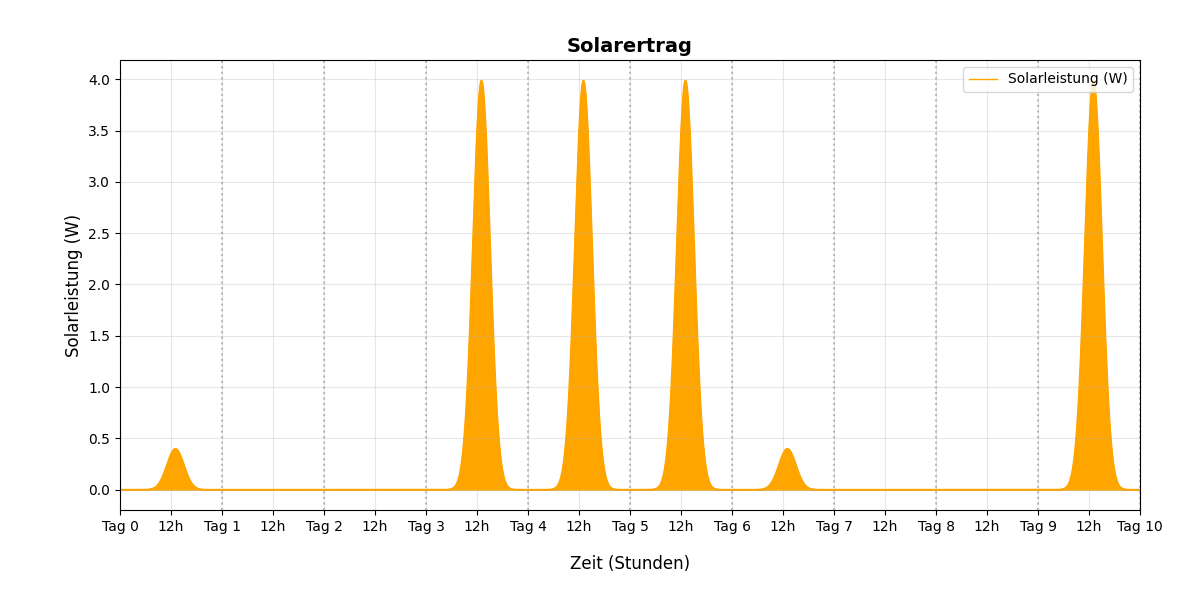
docs/Tests/SolarTests/Solarertrag_1.png
