Alexandros444/Datenbojen/docs/Tests/SolarTests/Solarertrag_Energieverbrauch.png

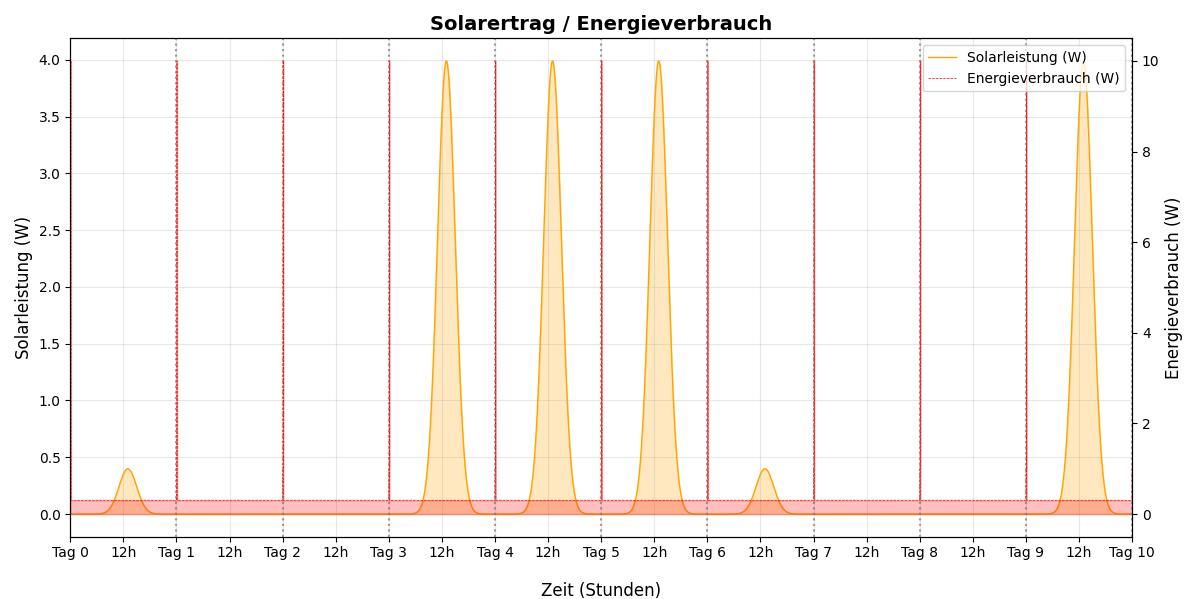
docs/Tests/SolarTests/Solarertrag_Energieverbrauch.png
