Alexandros444/Datenbojen/docs/Tests/SolarTests/Systemzustand_Leistungsbilanz.png

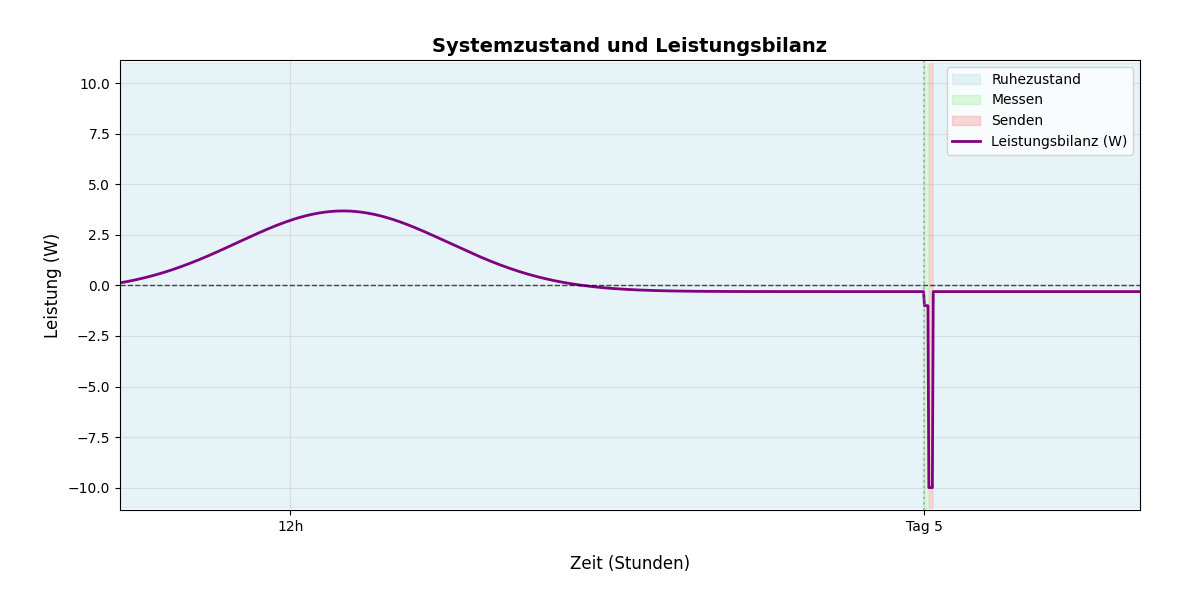
docs/Tests/SolarTests/Systemzustand_Leistungsbilanz.png
