Alexandros444/Datenbojen/docs/Tests/SystemTests/SystemTestLong1_energy.png

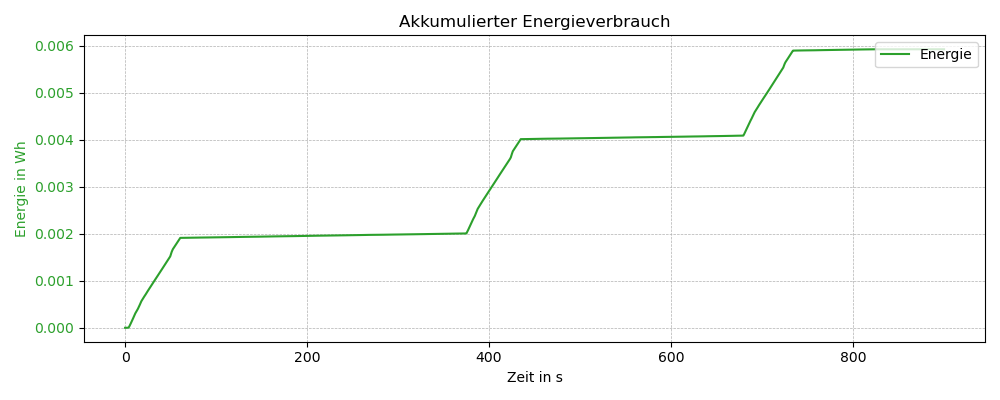
docs/Tests/SystemTests/SystemTestLong1_energy.png
