Alexandros444/Datenbojen/docs/Tests/SystemTests/SystemTestLong1_voltage_current.png

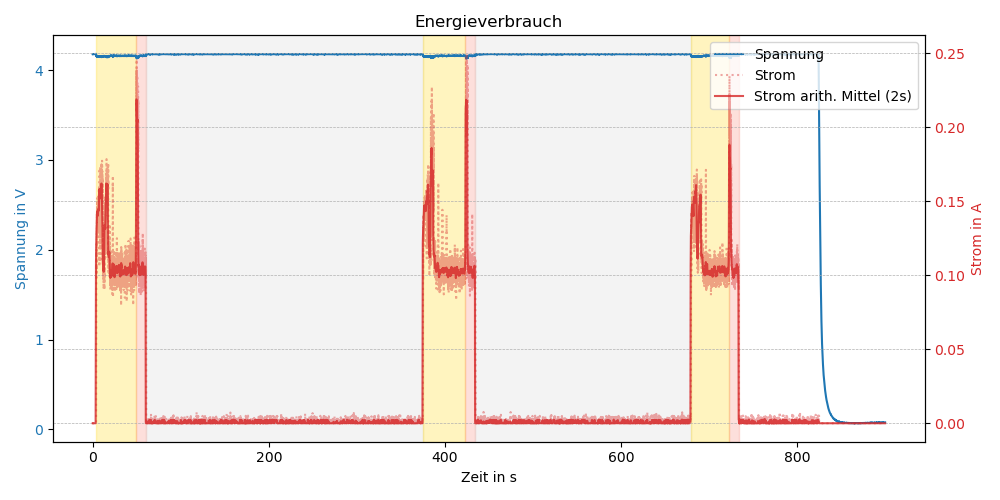
docs/Tests/SystemTests/SystemTestLong1_voltage_current.png
