Alexandros444/Datenbojen/docs/Tests/SystemTests/SystemTestLong2_energy.png

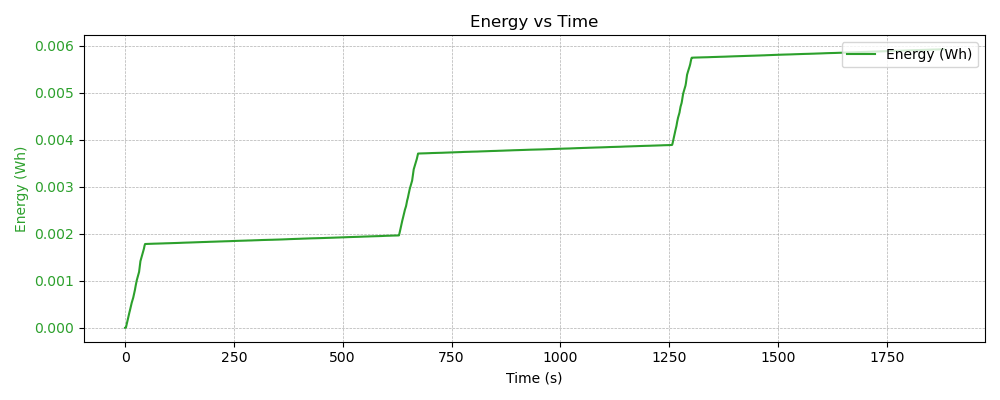
docs/Tests/SystemTests/SystemTestLong2_energy.png
