Alexandros444/Datenbojen/docs/Tests/SystemTests/SystemTestLong3_energy.png

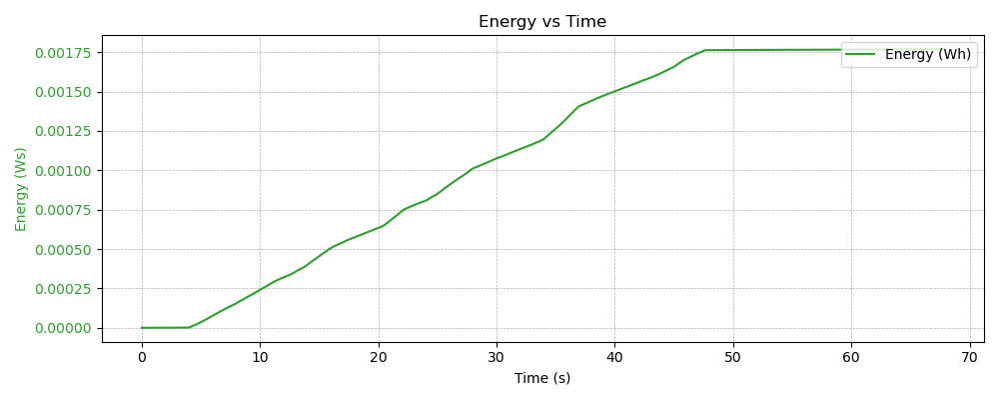
docs/Tests/SystemTests/SystemTestLong3_energy.png
