Alexandros444/Datenbojen/docs/Tests/SystemTests/SystemTestLong3_voltage_current.png

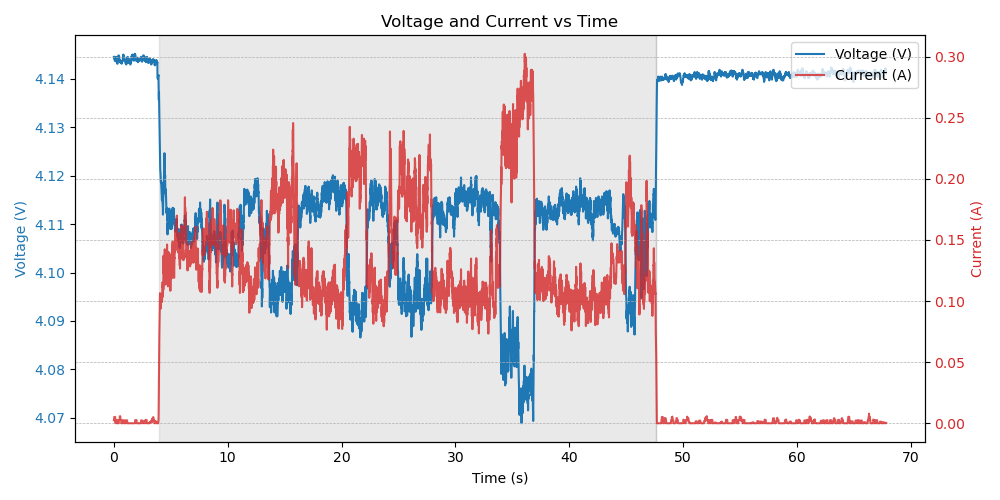
docs/Tests/SystemTests/SystemTestLong3_voltage_current.png
