Alexandros444/Datenbojen/docs/Tests/SystemTests/SystemTestLong4_energy.png

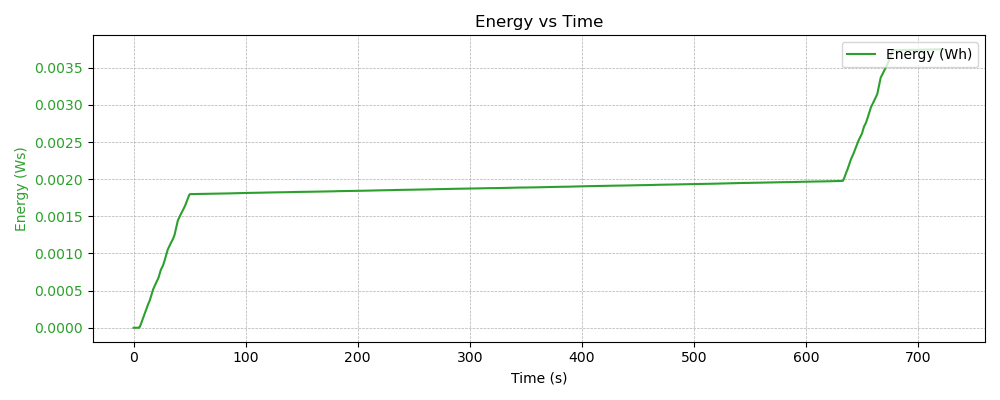
docs/Tests/SystemTests/SystemTestLong4_energy.png
