Alexandros444/Datenbojen/docs/Tests/SystemTests/SystemTestLong4_voltage_current.png

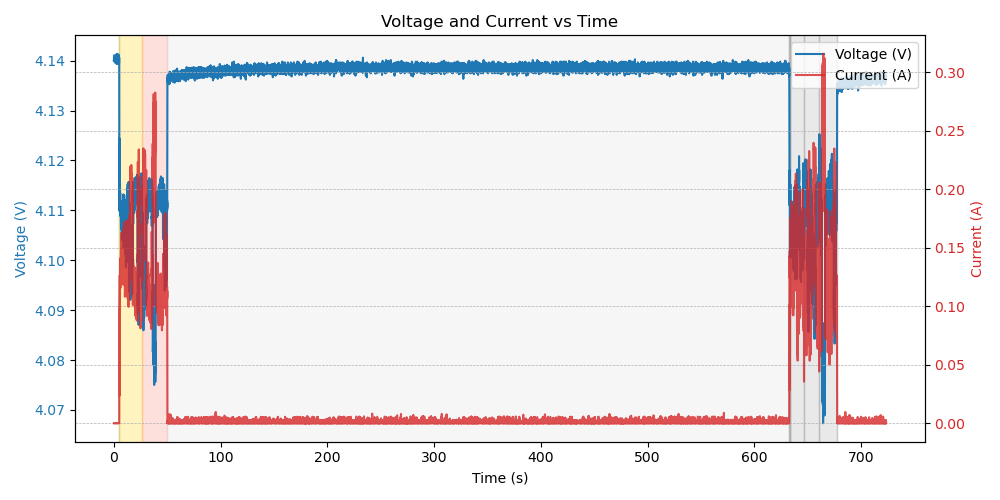
docs/Tests/SystemTests/SystemTestLong4_voltage_current.png
