Alexandros444/Datenbojen/docs/Tests/SystemTests/SystemTestLong5_energy.png

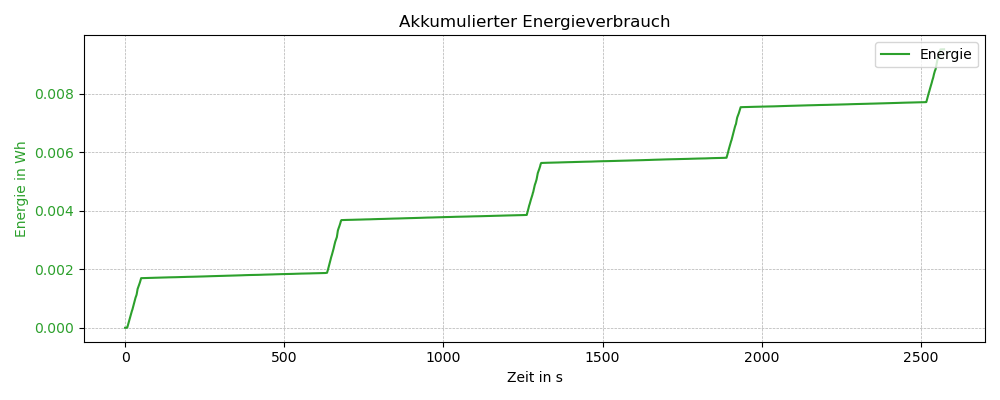
docs/Tests/SystemTests/SystemTestLong5_energy.png
