Alexandros444/Datenbojen/docs/Tests/SystemTests/SystemTestLong5_voltage_current.png

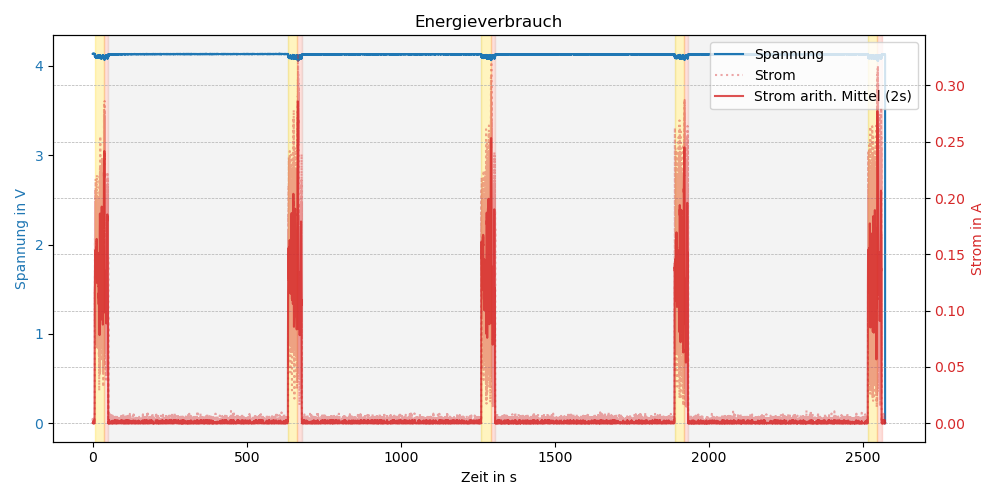
docs/Tests/SystemTests/SystemTestLong5_voltage_current.png
