Alexandros444/Datenbojen/src/ESP_GSM_TEST/images/qr.bmp

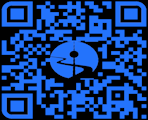
src/ESP_GSM_TEST/images/qr.bmp
