Alexandros444/Datenbojen/src/ESP_GSM_TEST/images/qr_24.bmp

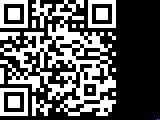
src/ESP_GSM_TEST/images/qr_24.bmp
