Alexandros444/Datenbojen/src/ESP_GSM_TEST/images/qr_blue.bmp

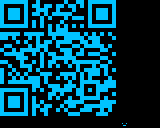
src/ESP_GSM_TEST/images/qr_blue.bmp
