Alexandros444/Datenbojen/src/ESP_GSM_TEST/images/qr_border.bmp

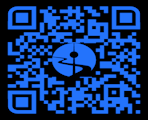
src/ESP_GSM_TEST/images/qr_border.bmp
