Alexandros444/Datenbojen/src/ESP_GSM_TEST/images/test24.bmp

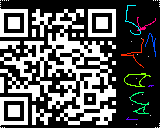
src/ESP_GSM_TEST/images/test24.bmp
