Alexandros444/Datenbojen/src/ESP_GSM_TEST/images/Unbenannt.bmp

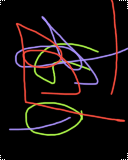
src/ESP_GSM_TEST/images/Unbenannt.bmp
