Alexandros444/Datenbojen/src/ESP_GSM_TEST/src/DFRobot_PH.cpp

/*!
 * @file DFRobot_PH.cpp
 * @brief Arduino library for Gravity: Analog pH Sensor / Meter Kit V2, SKU: SEN0161-V2
 *
 * @copyright   Copyright (c) 2010 DFRobot Co.Ltd (http://www.dfrobot.com)
 * @license     The MIT License (MIT)
 * @author [Jiawei Zhang](jiawei.zhang@dfrobot.com)
 * @version  V1.0
 * @date  2018-11-06
 * @url https://github.com/DFRobot/DFRobot_PH
 */


#if ARDUINO >= 100
#include "Arduino.h"
#else
#include "WProgram.h"
#endif

#include "DFRobot_PH.h"
#include <EEPROM.h>

#include "sensors_module.h"

#define EEPROM_write(address, p) {int i = 0; byte *pp = (byte*)&(p);for(; i < sizeof(p); i++) EEPROM.write(address+i, pp[i]);}
#define EEPROM_read(address, p)  {int i = 0; byte *pp = (byte*)&(p);for(; i < sizeof(p); i++) pp[i]=EEPROM.read(address+i);}

#define PHVALUEADDR PH_EEPROM_ADDRESS    //the start address of the pH calibration parameters stored in the EEPROM

char* DFRobot_PH::strupr(char* str) {
    if (str == NULL) return NULL;
    char *ptr = str;
    while (*ptr != ' ') {
        *ptr = toupper((unsigned char)*ptr);
        ptr++;
    }
    return str;
}

DFRobot_PH::DFRobot_PH()
{
    this->_temperature    = 25.0;
    this->_phValue        = 7.0;
    this->_acidVoltage    = 2032.44;    //buffer solution 4.0 at 25C
    this->_neutralVoltage = 1500.0;     //buffer solution 7.0 at 25C
    this->_voltage        = 1500.0;
}

DFRobot_PH::~DFRobot_PH()
{

}

void DFRobot_PH::begin()
{
    EEPROM_read(PHVALUEADDR, this->_neutralVoltage);  //load the neutral (pH = 7.0)voltage of the pH board from the EEPROM
    DPRINTF("Neutral Voltage loaded from EEPROM: %f mV\n", this->_neutralVoltage);
    if (EEPROM.read(PHVALUEADDR) == 0xFF && EEPROM.read(PHVALUEADDR + 1) == 0xFF && EEPROM.read(PHVALUEADDR + 2) == 0xFF && EEPROM.read(PHVALUEADDR + 3) == 0xFF) {
        this->_neutralVoltage = 1500.0;  // new EEPROM, write typical voltage
        EEPROM_write(PHVALUEADDR, this->_neutralVoltage);
    }

    EEPROM_read(PHVALUEADDR + 4, this->_acidVoltage);//load the acid (pH = 4.0) voltage of the pH board from the EEPROM
    DPRINTF("Acid Voltage loaded from EEPROM: %f mV\n", this->_acidVoltage);

    if (EEPROM.read(PHVALUEADDR + 4) == 0xFF && EEPROM.read(PHVALUEADDR + 5) == 0xFF && EEPROM.read(PHVALUEADDR + 6) == 0xFF && EEPROM.read(PHVALUEADDR + 7) == 0xFF) {
        this->_acidVoltage = 2032.44;  // new EEPROM, write typical voltage
        EEPROM_write(PHVALUEADDR + 4, this->_acidVoltage);
    }

    if (_neutralVoltage == 0.0 || _acidVoltage == 0.0) {
        Serial.println(F("Neutral or Acid Voltage is zero, resetting EEPROM to default values."));
        resetEEPROM(); // Reset EEPROM to default values if neutral or acid voltage is zero
    }

}
    void DFRobot_PH::resetEEPROM() {
    this->_neutralVoltage = 1500.0;  // reset to default value
    this->_acidVoltage = 2032.44;     // reset to default value
    EEPROM_write(PHVALUEADDR, this->_neutralVoltage);
    EEPROM_write(PHVALUEADDR+4, this->_acidVoltage);
    Serial.println(F("EEPROM reset to default values."));
}


/***
 * @fn readPH
 * @brief Convert voltage to PH with temperature compensation
 * @note voltage to pH value, with temperature compensation
 * @param voltage     : mV
 * @param temperature : Water temperature
 * @return The PH value
 */

float DFRobot_PH::readPH(float voltage, float temperature)
{
    float slope = (7.0 - 4.0) / ((this->_neutralVoltage - 1500.0) / 3.0 - (this->_acidVoltage - 1500.0) / 3.0);  // two point: (_neutralVoltage,7.0),(_acidVoltage,4.0)
    float intercept =  7.0 - slope*(this->_neutralVoltage-1500.0)/3.0;
    //Serial.print("slope:");
    //Serial.print(slope);
    //Serial.print(",intercept:");
    //Serial.println(intercept);
    this->_phValue = slope*(voltage-1500.0)/3.0+intercept;  //y = k*x + b
#ifdef DEBUG_PRINT
    Serial.printf("Reading PH value with voltage: %f mV, temperature: %f C\n", voltage, temperature);
    Serial.printf("Neutral Voltage: %f mV, Acid Voltage: %f mV\n", this->_neutralVoltage, this->_acidVoltage);
    Serial.printf("slope: %f, intercept: %f, calculated pH value: %f\n", slope, intercept, this->_phValue);
#endif
    return _phValue;
}


void DFRobot_PH::calibration(float voltage, float temperature,char* cmd)
{
    this->_voltage = voltage;
    this->_temperature = temperature;
    String sCmd = String(cmd);
    sCmd.toUpperCase();
    phCalibration(cmdParse(sCmd.c_str()));  // if received Serial CMD from the serial monitor, enter into the calibration mode
}

void DFRobot_PH::calibration(float voltage, float temperature)
{
    this->_voltage = voltage;
    this->_temperature = temperature;
    if(cmdSerialDataAvailable() > 0){
        phCalibration(cmdParse());  // if received Serial CMD from the serial monitor, enter into the calibration mode
    }
}

boolean DFRobot_PH::cmdSerialDataAvailable()
{
    char cmdReceivedChar;
    static unsigned long cmdReceivedTimeOut = millis();
    while(Serial.available()>0){
        if(millis() - cmdReceivedTimeOut > 500U){
            this->_cmdReceivedBufferIndex = 0;
            memset(this->_cmdReceivedBuffer,0,(ReceivedBufferLength));
        }
        cmdReceivedTimeOut = millis();
        cmdReceivedChar = Serial.read();
        if (cmdReceivedChar == '\n' || this->_cmdReceivedBufferIndex==ReceivedBufferLength-1){
            this->_cmdReceivedBufferIndex = 0;
            strupr(this->_cmdReceivedBuffer);
            return true;
        }else{
            this->_cmdReceivedBuffer[this->_cmdReceivedBufferIndex] = cmdReceivedChar;
            this->_cmdReceivedBufferIndex++;
        }
    }
    return false;
}

byte DFRobot_PH::cmdParse(const char* cmd)
{
    byte modeIndex = 0;
    if(strstr(cmd, "ENTERPH")      != NULL){
        modeIndex = 1;
    }else if(strstr(cmd, "EXITPH") != NULL){
        modeIndex = 3;
    }else if(strstr(cmd, "CALPH")  != NULL){
        modeIndex = 2;
    }
    return modeIndex;
}

byte DFRobot_PH::cmdParse()
{
    byte modeIndex = 0;
    if(strstr(this->_cmdReceivedBuffer, "ENTERPH")      != NULL){
        modeIndex = 1;
    }else if(strstr(this->_cmdReceivedBuffer, "EXITPH") != NULL){
        modeIndex = 3;
    }else if(strstr(this->_cmdReceivedBuffer, "CALPH")  != NULL){
        modeIndex = 2;
    }
    return modeIndex;
}

void DFRobot_PH::phCalibration(byte mode)
{
    char *receivedBufferPtr;
    static boolean phCalibrationFinish  = 0;
    static boolean enterCalibrationFlag = 0;
    switch(mode){
        case 0:
        if(enterCalibrationFlag){
            Serial.println(F(">>>Command Error<<<"));
        }
        break;

        case 1:
        enterCalibrationFlag = 1;
        phCalibrationFinish  = 0;
        Serial.println();
        Serial.println(F(">>>Enter PH Calibration Mode<<<"));
        Serial.println(F(">>>Please put the probe into the 4.0 or 7.0 standard buffer solution<<<"));
        Serial.println();
        break;

        case 2:
        if(enterCalibrationFlag){
            if((this->_voltage>1322)&&(this->_voltage<1678)){        // buffer solution:7.0{
                Serial.println();
                Serial.print(F(">>>Buffer Solution:7.0"));
                this->_neutralVoltage =  this->_voltage;
                Serial.println(F(",Send EXITPH to Save and Exit<<<"));
                Serial.println();
                phCalibrationFinish = 1;
            }else if((this->_voltage>1854)&&(this->_voltage<2210)){  //buffer solution:4.0
                Serial.println();
                Serial.print(F(">>>Buffer Solution:4.0"));
                this->_acidVoltage =  this->_voltage;
                Serial.println(F(",Send EXITPH to Save and Exit<<<")); 
                Serial.println();
                phCalibrationFinish = 1;
            }else{
                Serial.println();
                Serial.print(F(">>>Buffer Solution Error Try Again<<<"));
                Serial.println();                                    // not buffer solution or faulty operation
                phCalibrationFinish = 0;
            }
        }
        break;

        case 3:
        if(enterCalibrationFlag){
            Serial.println();
            if(phCalibrationFinish){
                if((this->_voltage>1322)&&(this->_voltage<1678)){

                    EEPROM_write(PHVALUEADDR, this->_neutralVoltage);
                }else if((this->_voltage>1854)&&(this->_voltage<2210)){
                    EEPROM_write(PHVALUEADDR+4, this->_acidVoltage);
                }
                Serial.print(F(">>>Calibration Successful"));
            }else{
                Serial.print(F(">>>Calibration Failed"));
            }
            Serial.println(F(",Exit PH Calibration Mode<<<"));
            Serial.println();
            phCalibrationFinish  = 0;
            enterCalibrationFlag = 0;
        }
        break;
    }
}
