Alexandros444/Datenbojen/src/ESP_GSM_TEST/include/wifi_module.h

#ifndef WIFI_MODULE_H
#define WIFI_MODULE_H

#include <WiFi.h>
#include <HTTPClient.h>
#include <ArduinoJson.h>
#include "sensors_module.h"
#include "gsm_module.h"

class wifi_module {
private:
    const char* ssid = "FRITZ!Box 6660 Cable KW";
    const char* password = "15730960856266684059";
    String serverName = "http://jserv.ddns.net:8080/update-sensor";
    sensors_module *sensors;
    gsm_module *gsm;
public:
    wifi_module(){};
    ~wifi_module(){};
    void begin(sensors_module* sensors, gsm_module* gsm);
    int sendData();
    void turn_off(){ WiFi.disconnect(true); WiFi.mode(WIFI_OFF); }
};


#endif
