Alexandros444/Datenbojen/docs/img/Entwurf/IMG_7579.JPG

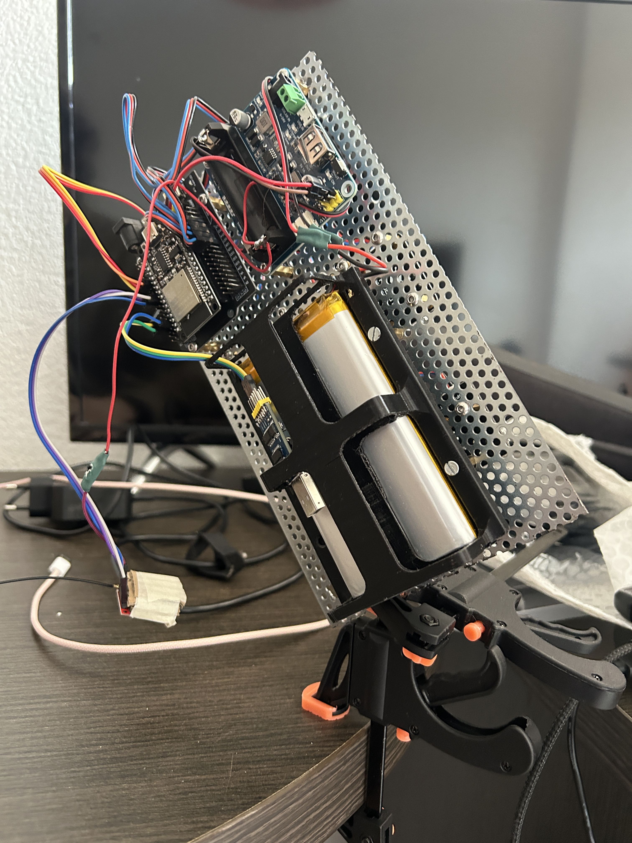
docs/img/Entwurf/IMG_7579.JPG
